e3w2q/Pangaea-keyboard/images/0a40776e85302190b7db8250a09605896cdc25e2c0a9c59730956f0daec5297e.jpg

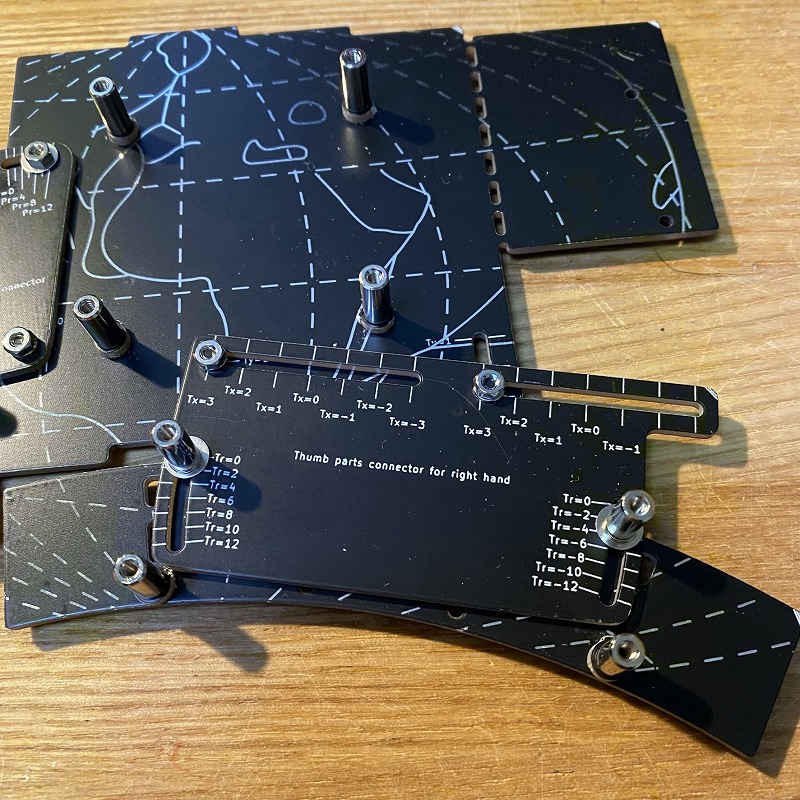
images/0a40776e85302190b7db8250a09605896cdc25e2c0a9c59730956f0daec5297e.jpg
