e3w2q/Pangaea-keyboard/images/3de5a38e3a6196bc59657bb92bddd8e8714a5d8ba0b0069f44ba43b166290112.jpg

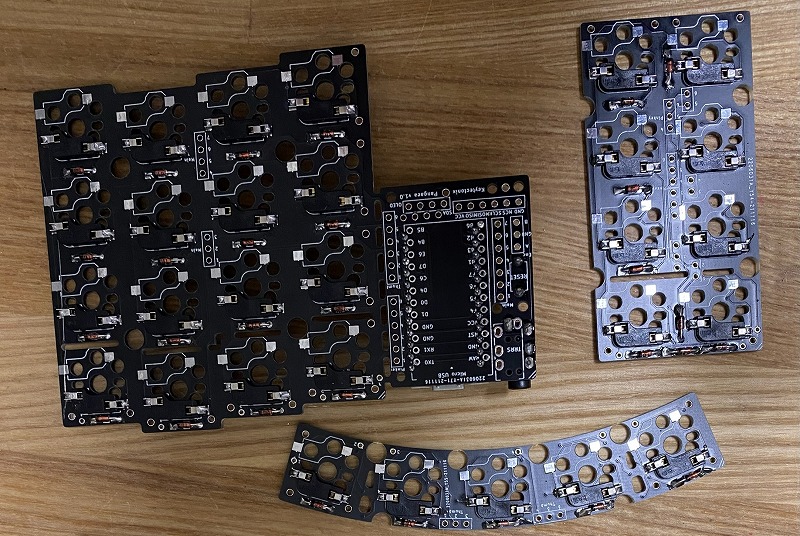
images/3de5a38e3a6196bc59657bb92bddd8e8714a5d8ba0b0069f44ba43b166290112.jpg
