e3w2q/Pangaea-keyboard/images/6bcce53f80934620b18218db5a653d9b1c7b2bb7c57de2113d1901ce5737880e.jpg

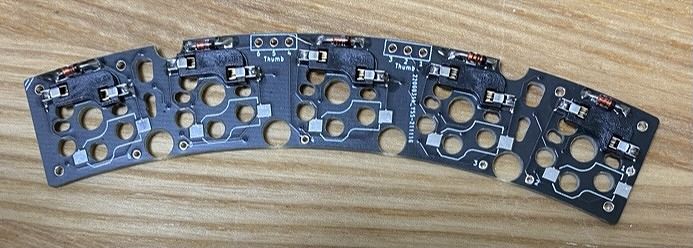
images/6bcce53f80934620b18218db5a653d9b1c7b2bb7c57de2113d1901ce5737880e.jpg
