e3w2q/Pangaea-keyboard/images/12b5d017e92538700fd86b66f8f17ba5b7837069fc4d05f0cf9e0c62a58a4044.jpg

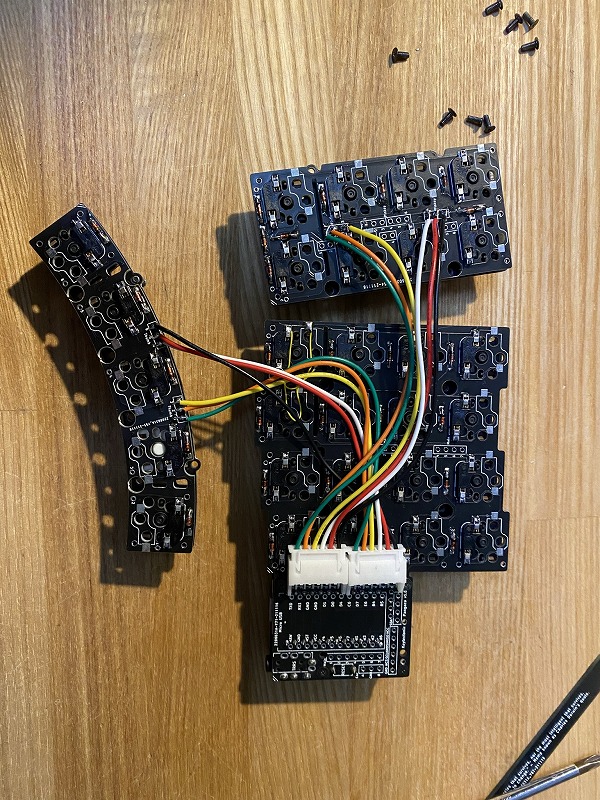
images/12b5d017e92538700fd86b66f8f17ba5b7837069fc4d05f0cf9e0c62a58a4044.jpg
