e3w2q/Pangaea-keyboard/images/13a6e4abe06fdf55e29f08c79a0a2a02d93426b52d6df6399b1b247043b9f3ee.jpg

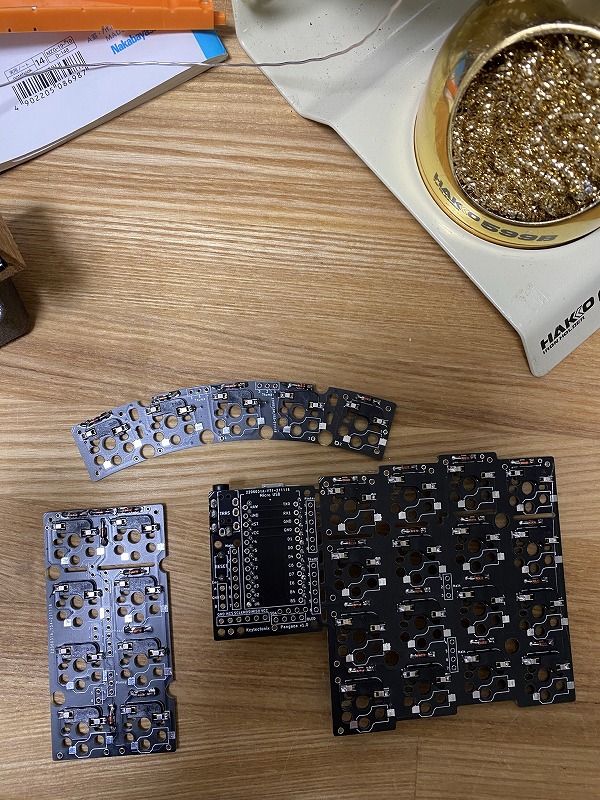
images/13a6e4abe06fdf55e29f08c79a0a2a02d93426b52d6df6399b1b247043b9f3ee.jpg
