e3w2q/Pangaea-keyboard/images/27a483f2cba5d88a76916c5f78700c6e7530f33930280dae4c5f8cfa2cd41bf4.jpg

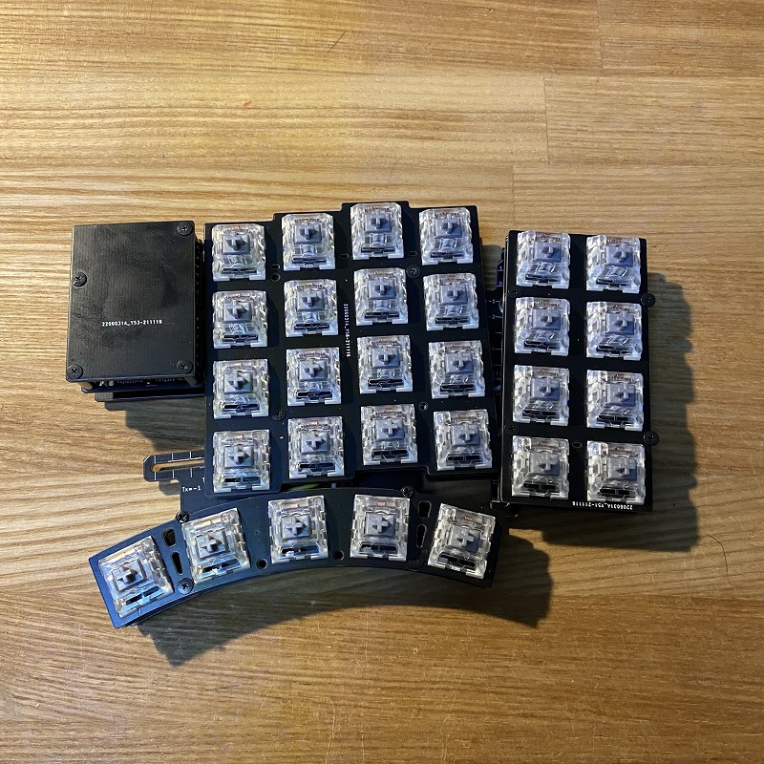
images/27a483f2cba5d88a76916c5f78700c6e7530f33930280dae4c5f8cfa2cd41bf4.jpg
