e3w2q/Pangaea-keyboard/images/60b84ec0d109d0ff8fc8ae6644fc2632dbbb4cfb449918cca01a9c03fa35eddc.jpg

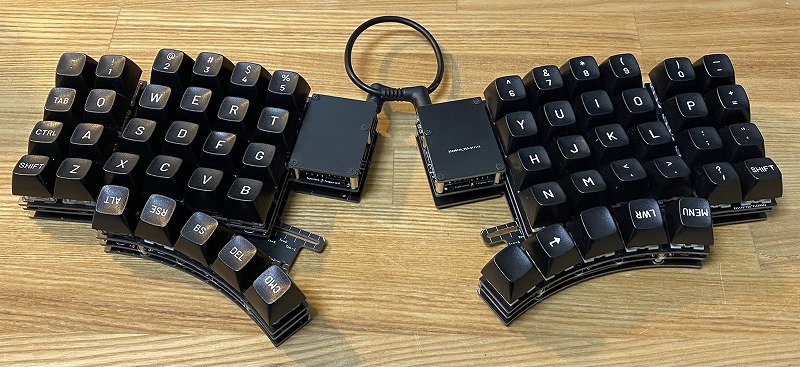
images/60b84ec0d109d0ff8fc8ae6644fc2632dbbb4cfb449918cca01a9c03fa35eddc.jpg
