e3w2q/Pangaea-keyboard/images/063d4ac2fd48cc3513ddb311a2d0394e6f6cdcdaa0d06b1ff0ed7a4a48f6335a.png

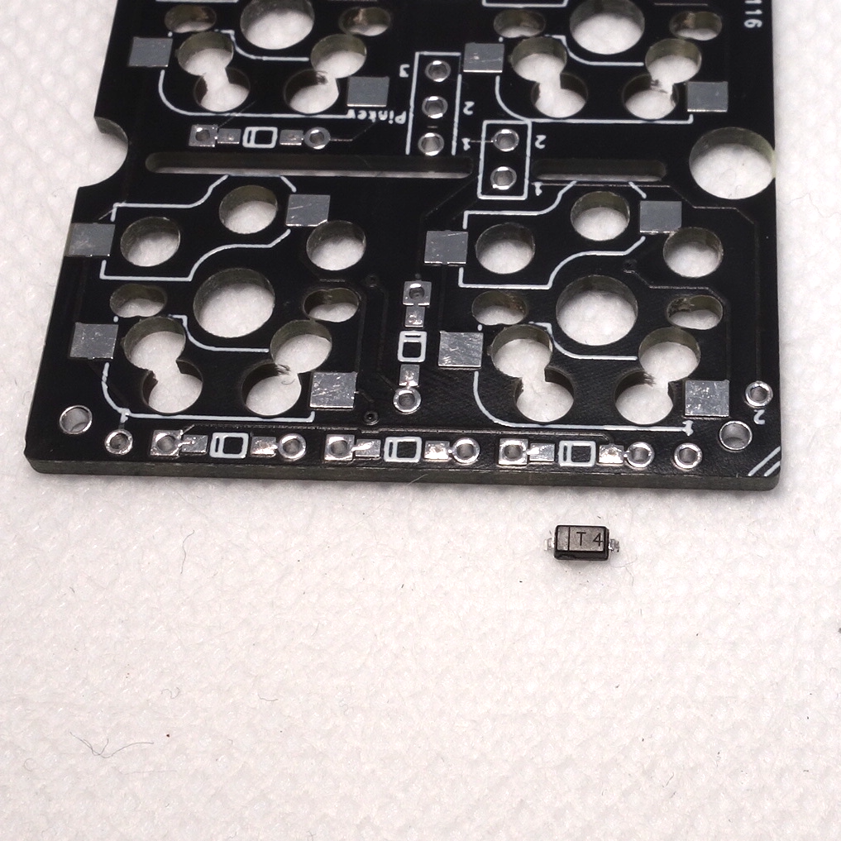
images/063d4ac2fd48cc3513ddb311a2d0394e6f6cdcdaa0d06b1ff0ed7a4a48f6335a.png
