e3w2q/Pangaea-keyboard/images/67ab104578fdced3b91575ca5da068cccac055a47365c25860a59a9be2ea70eb.jpg

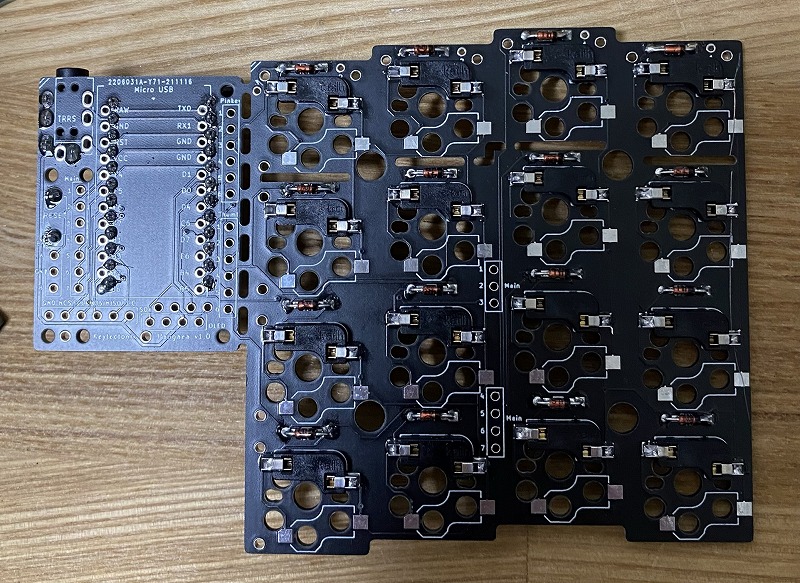
images/67ab104578fdced3b91575ca5da068cccac055a47365c25860a59a9be2ea70eb.jpg
