e3w2q/Pangaea-keyboard/images/92ce04aa23efa934309d4d564b36739e237e41bc6f97a7b27b288d3fab1753d2.jpg

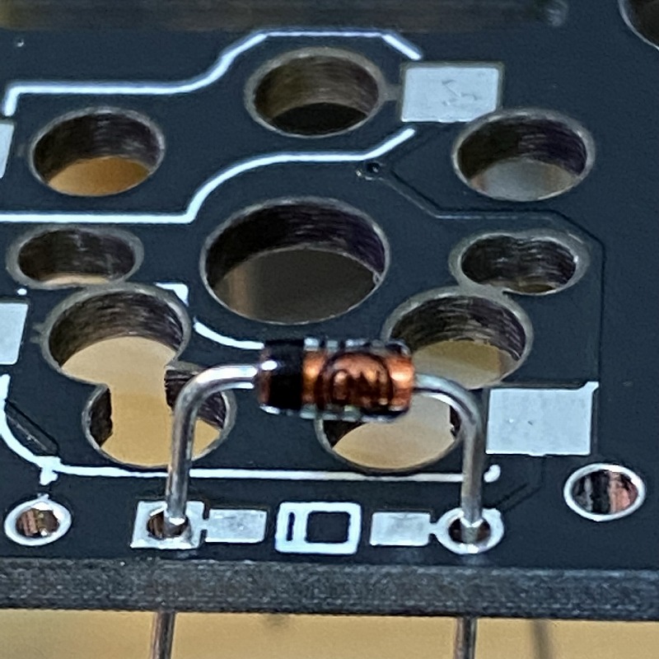
images/92ce04aa23efa934309d4d564b36739e237e41bc6f97a7b27b288d3fab1753d2.jpg
