e3w2q/Pangaea-keyboard/images/265e11b32b4d3e79da52cd56ff77c7da640a06a07a428f72cf4426d7e051b964.jpg

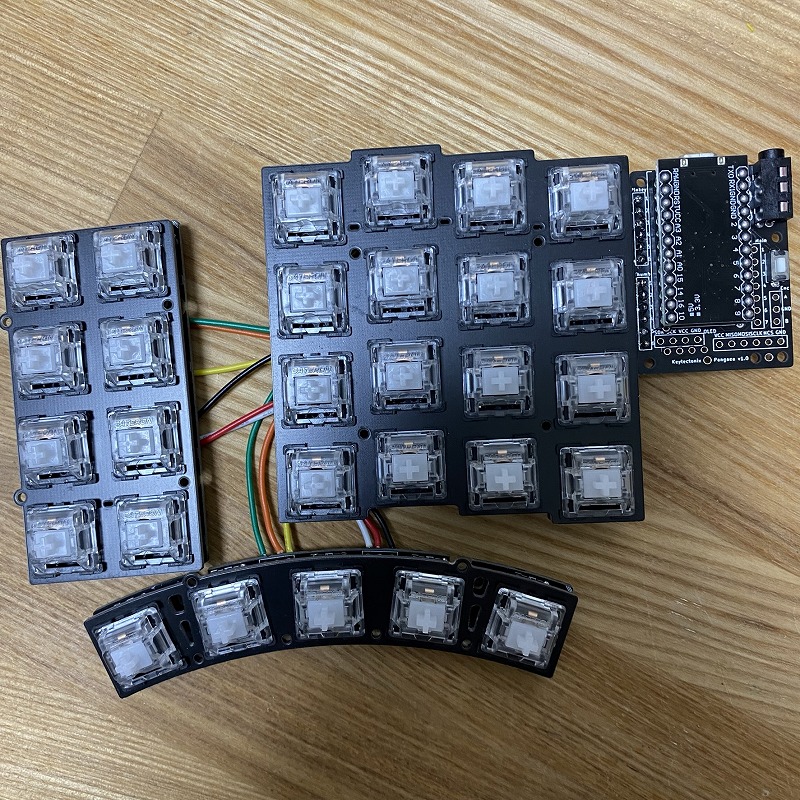
images/265e11b32b4d3e79da52cd56ff77c7da640a06a07a428f72cf4426d7e051b964.jpg
