e3w2q/Pangaea-keyboard/images/1651ed1e01f4abee588f21293dc81c73a5ee6cbbf57d6cacc2041a118a28469f.png

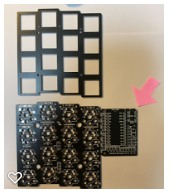
images/1651ed1e01f4abee588f21293dc81c73a5ee6cbbf57d6cacc2041a118a28469f.png
