e3w2q/Pangaea-keyboard/images/4654de285b3f48fc8ee407a733680955d16ebc803d51c34f99765b41f4ffe5e8.jpg

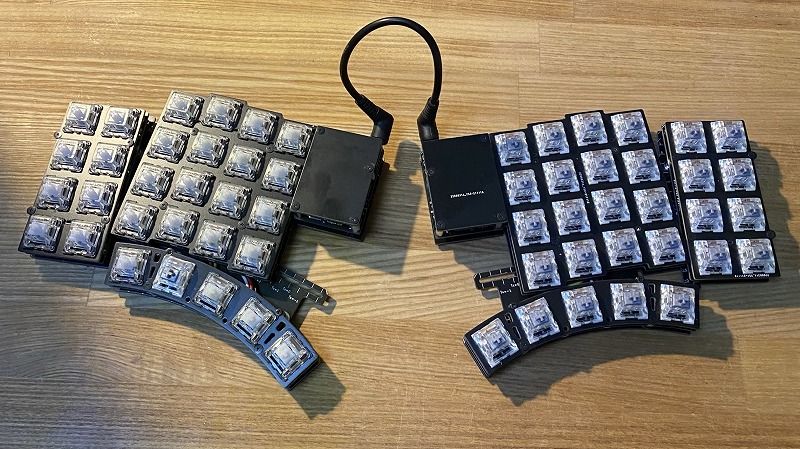
images/4654de285b3f48fc8ee407a733680955d16ebc803d51c34f99765b41f4ffe5e8.jpg
