e3w2q/Pangaea-keyboard/images/7964ab9c6218b75f5bff196d36406f74450f77bdc9f00a825abc09a86ed46ff9.jpg

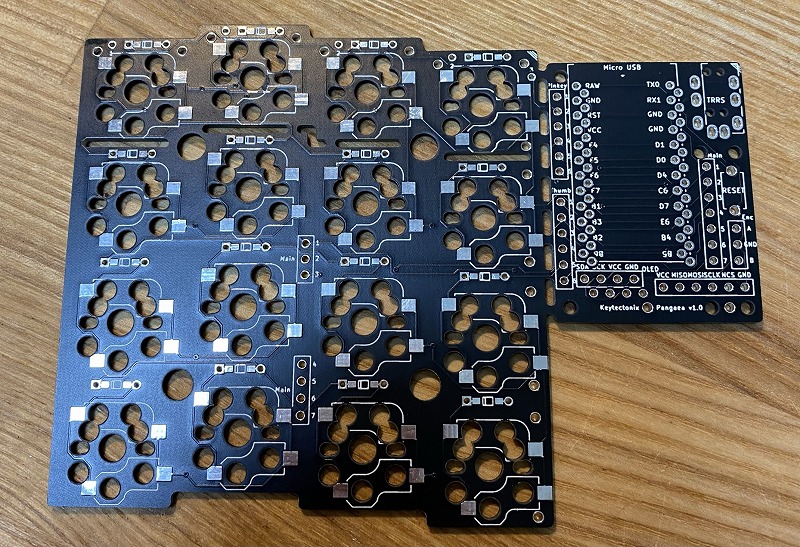
images/7964ab9c6218b75f5bff196d36406f74450f77bdc9f00a825abc09a86ed46ff9.jpg
