e3w2q/Pangaea-keyboard/images/15282b31c44fe6ef8862abb38c801023dfbcf05c0192a9374a89fd2af4d39e05.jpg

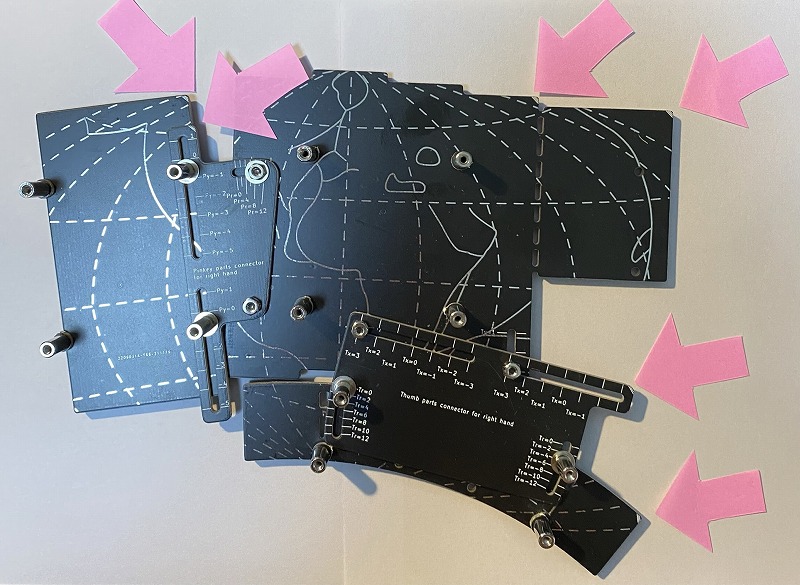
images/15282b31c44fe6ef8862abb38c801023dfbcf05c0192a9374a89fd2af4d39e05.jpg
