e3w2q/Pangaea-keyboard/images/0477079cc677149b845d37c62d5b3265d9a6df82ff215ac21fa13e02ba05858f.png

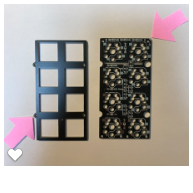
images/0477079cc677149b845d37c62d5b3265d9a6df82ff215ac21fa13e02ba05858f.png
