e3w2q/Pangaea-keyboard/images/0908893b698defab134e45d7c74e45a14b349f7c2ef67a782a992773b4fd4b19.jpg

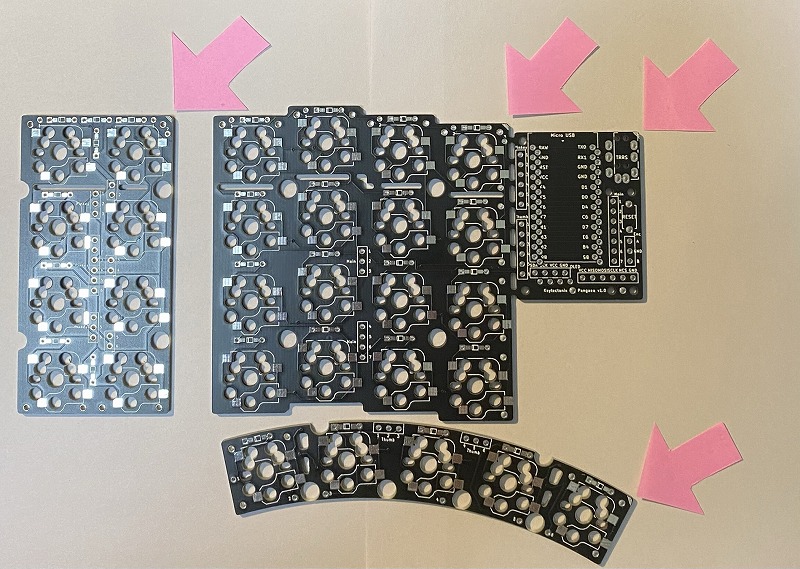
images/0908893b698defab134e45d7c74e45a14b349f7c2ef67a782a992773b4fd4b19.jpg
