e3w2q/Pangaea-keyboard/images/965143ae04164a4b04ba0ac7c3d9436b181fd4520849607ac215952e7ac29c34.jpg

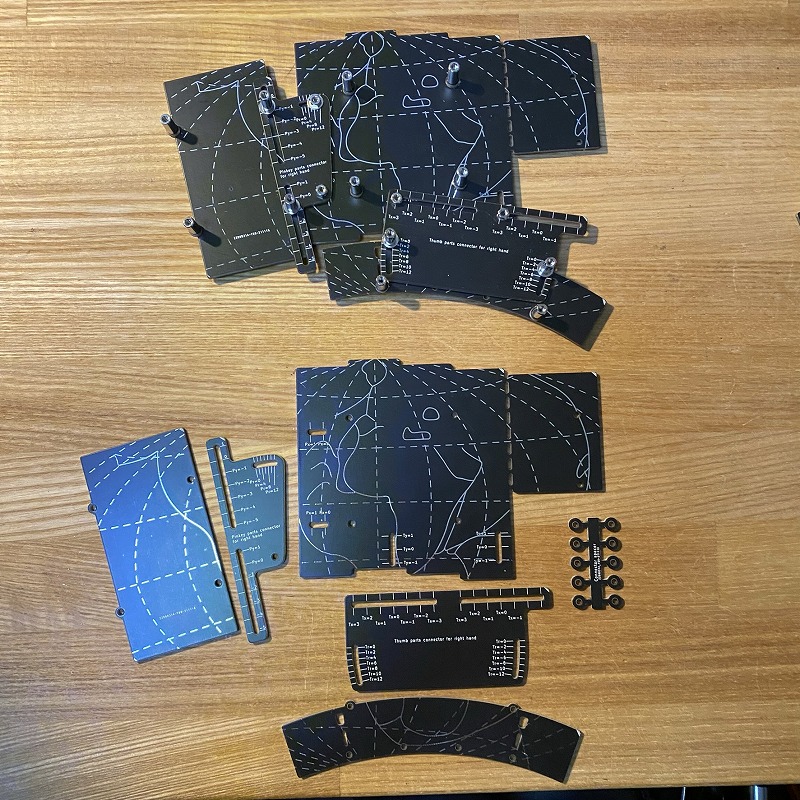
images/965143ae04164a4b04ba0ac7c3d9436b181fd4520849607ac215952e7ac29c34.jpg
