e3w2q/Pangaea-keyboard/images/ae8b663de61265fc9e2a7c73a48820bda330f6d65dd7c69996d7fd06cbfcfd85.jpg

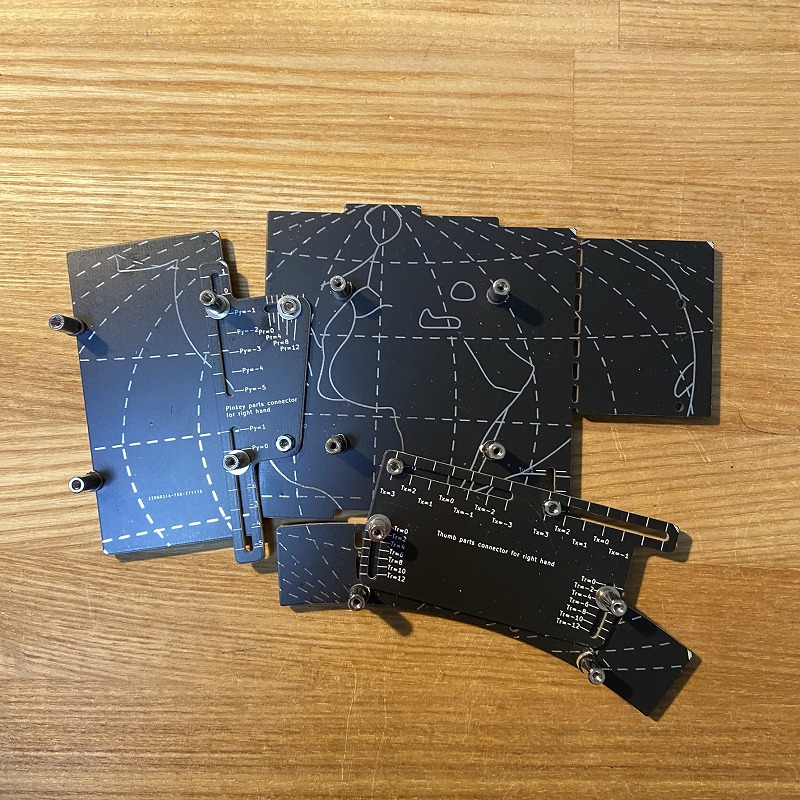
images/ae8b663de61265fc9e2a7c73a48820bda330f6d65dd7c69996d7fd06cbfcfd85.jpg
