e3w2q/Pangaea-keyboard/images/b1e843c930b5d5a4a3331d23bac49f055a0c1e8cba4a9a129905668647902217.jpg

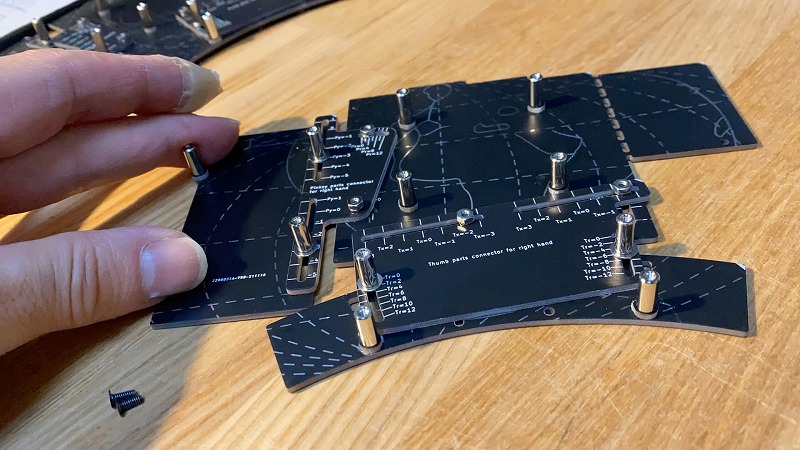
images/b1e843c930b5d5a4a3331d23bac49f055a0c1e8cba4a9a129905668647902217.jpg
