e3w2q/Pangaea-keyboard/images/d9ac8d5ce5317f976f2c17d7057b1348e89b5a3f5772f75e08f726dfaba970bf.jpg

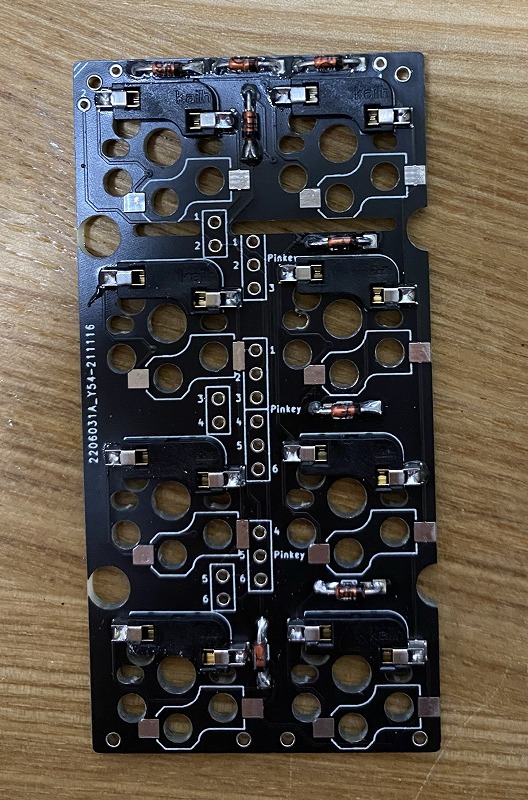
images/d9ac8d5ce5317f976f2c17d7057b1348e89b5a3f5772f75e08f726dfaba970bf.jpg
