e3w2q/Pangaea-keyboard/images/d27c56cb22e5b8cc0af3af3c9623e22fa6d8d71f143a236a87373760cafe7f19.png

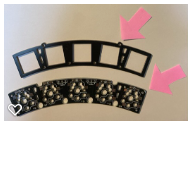
images/d27c56cb22e5b8cc0af3af3c9623e22fa6d8d71f143a236a87373760cafe7f19.png
