e3w2q/Pangaea-keyboard/images/d383ae3981553dc0fcf38ef8d6c3e6acfb4eb097b5aa347cb851257b4d14731c.jpg

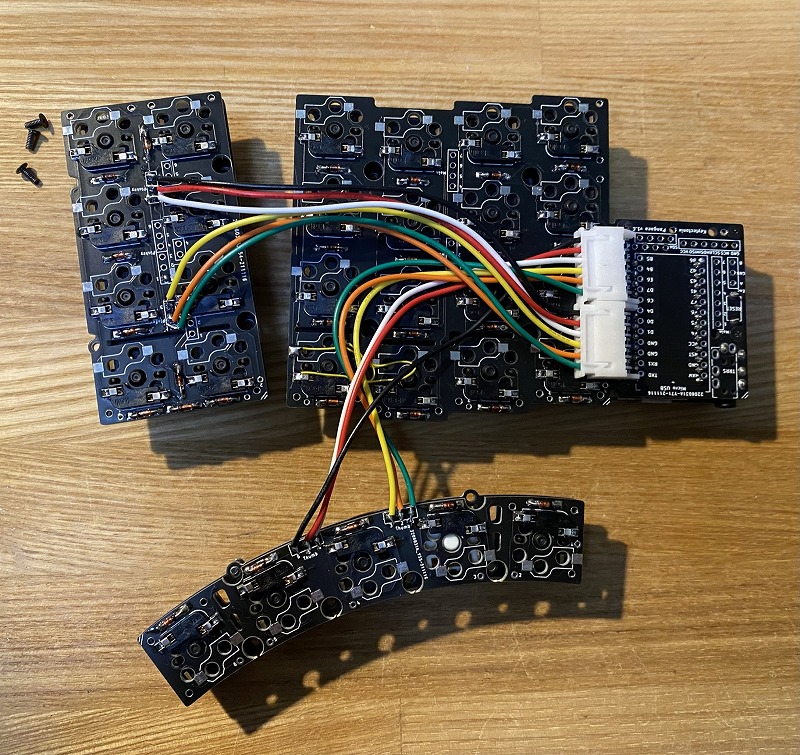
images/d383ae3981553dc0fcf38ef8d6c3e6acfb4eb097b5aa347cb851257b4d14731c.jpg
