e3w2q/Pangaea-keyboard/images/d52466fd30a9bd447ba011db17c6af2e1d6d6b381e681eb9b976b4c6a248406f.jpg

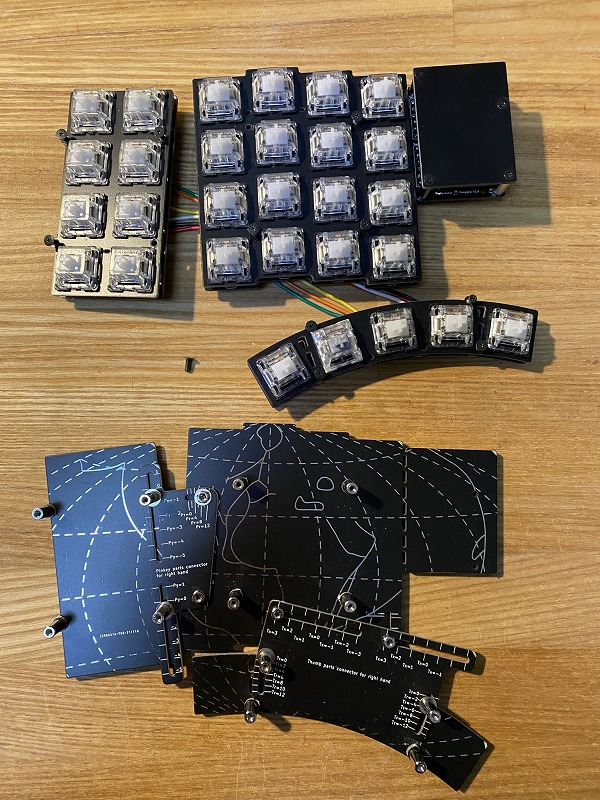
images/d52466fd30a9bd447ba011db17c6af2e1d6d6b381e681eb9b976b4c6a248406f.jpg
