e3w2q/Pangaea-keyboard/images/db102ce236ea3b06e92ff9be887bdc986abb1811367a4291042e3f9954540378.png

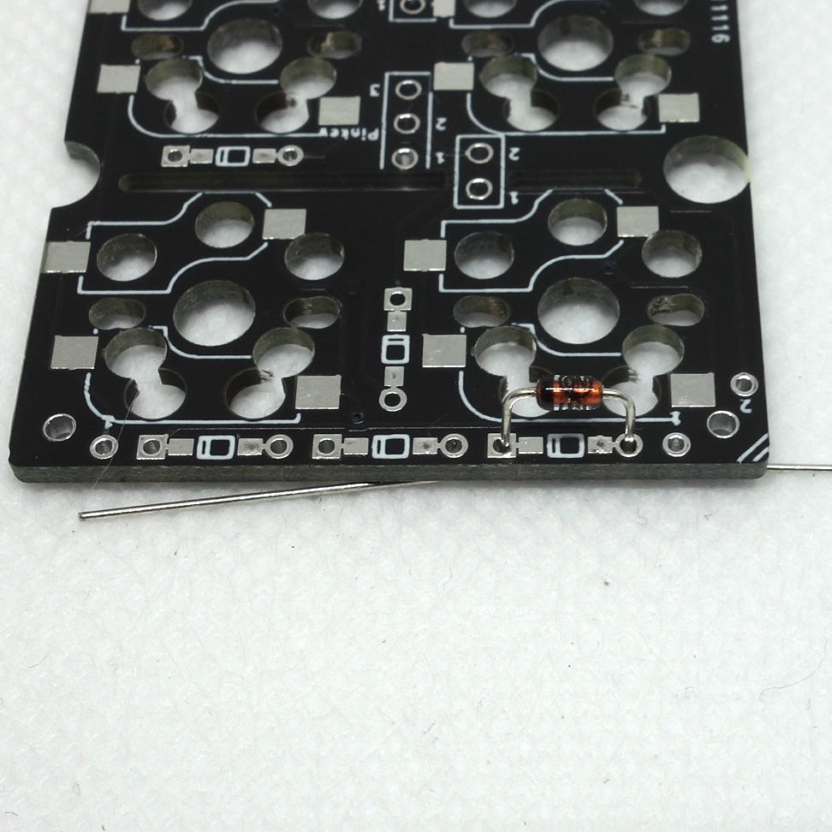
images/db102ce236ea3b06e92ff9be887bdc986abb1811367a4291042e3f9954540378.png
