e3w2q/Pangaea-keyboard/images/DSCF6513.jpeg

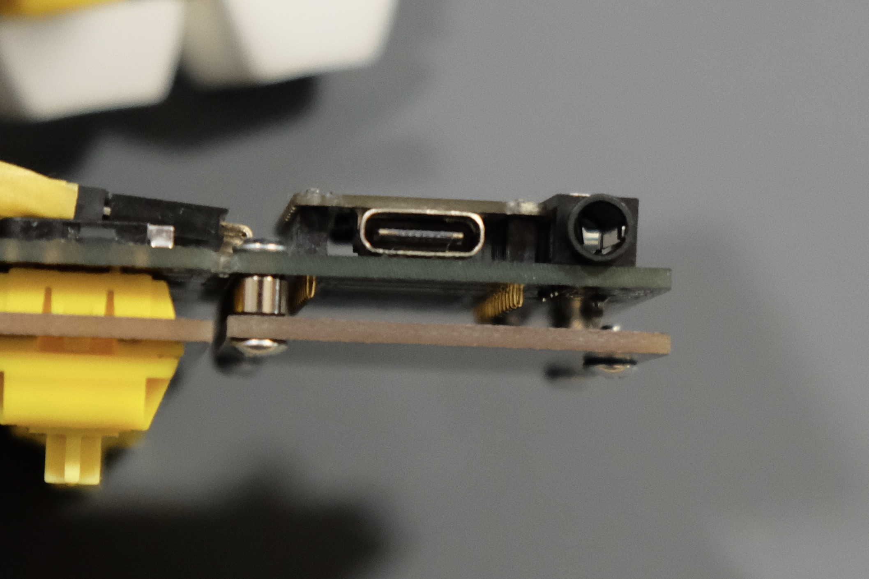
images/DSCF6513.jpeg
