e3w2q/Pangaea-keyboard/images/DSCF8427.jpg

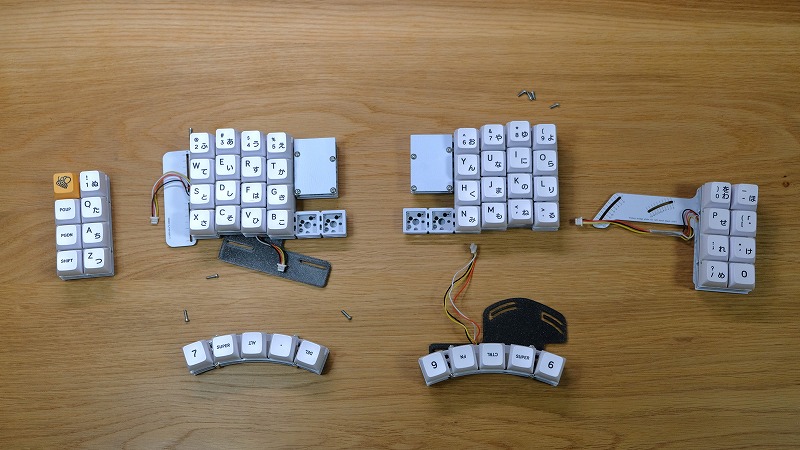
images/DSCF8427.jpg
