e3w2q/Pangaea-keyboard/images/DSCF8429.jpg

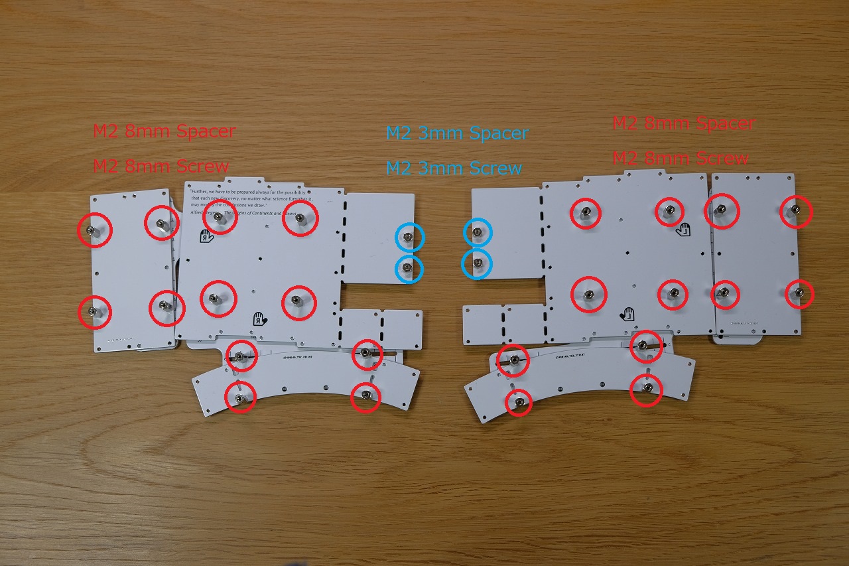
images/DSCF8429.jpg
