e3w2q/Pangaea-keyboard/images/DSCF8474.jpg

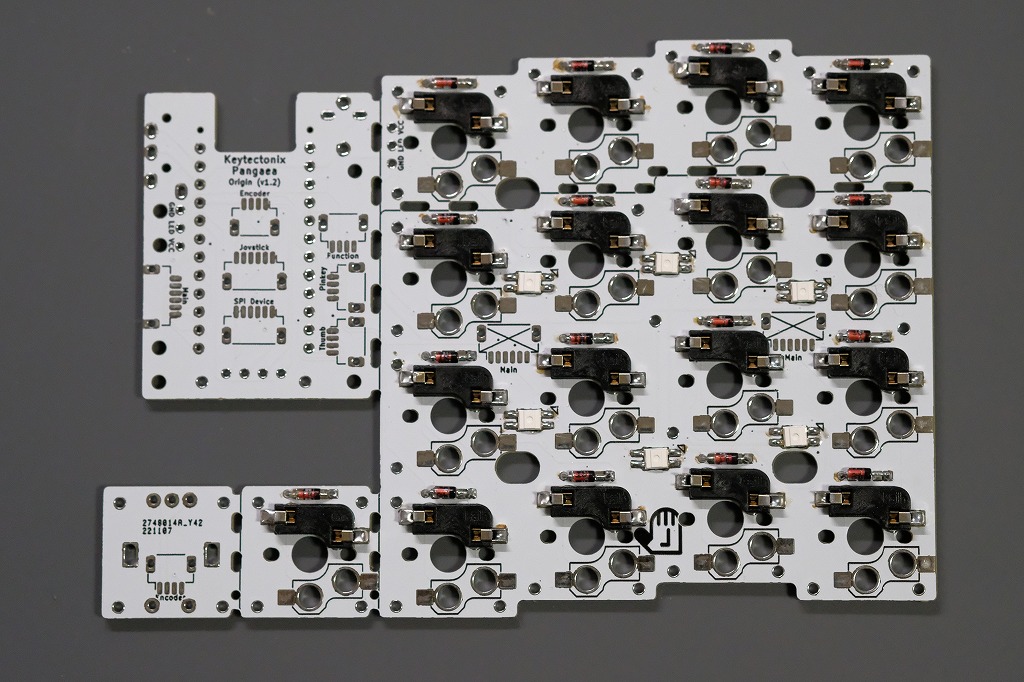
images/DSCF8474.jpg
