e3w2q/Pangaea-keyboard/images/DSCF8711.jpg

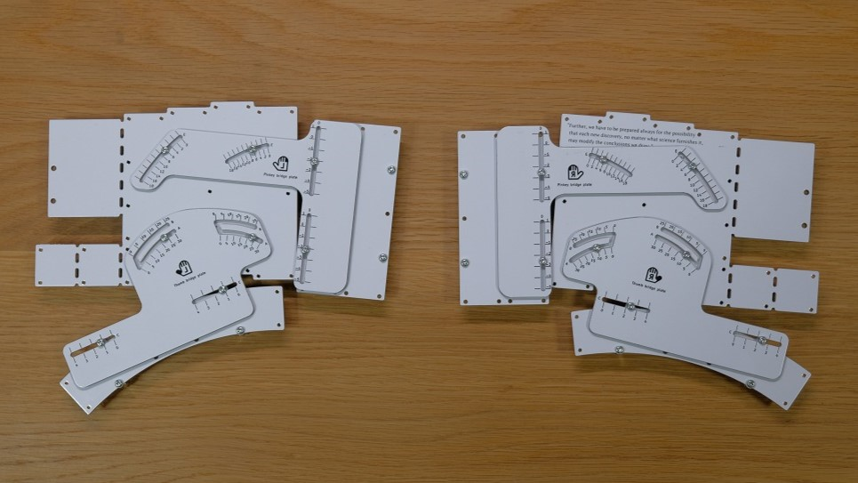
images/DSCF8711.jpg
