e3w2q/Pangaea-keyboard/images/e3-all.jpg

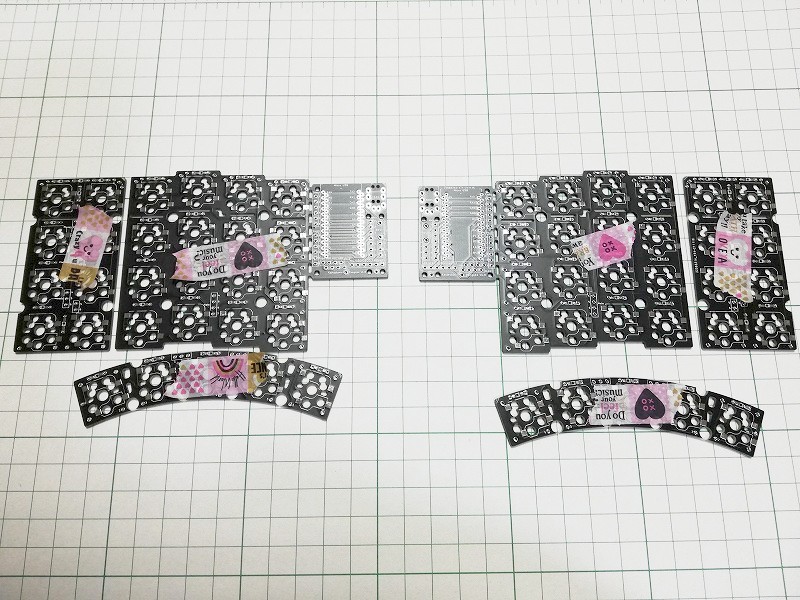
images/e3-all.jpg
