e3w2q/Pangaea-keyboard/images/e3-left.jpg

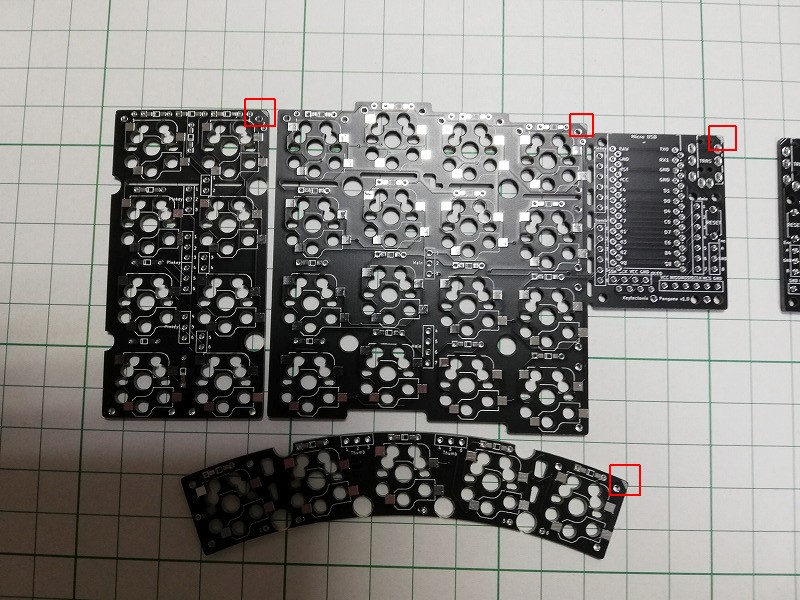
images/e3-left.jpg
