e3w2q/Pangaea-keyboard/images/e3-promicro.jpg

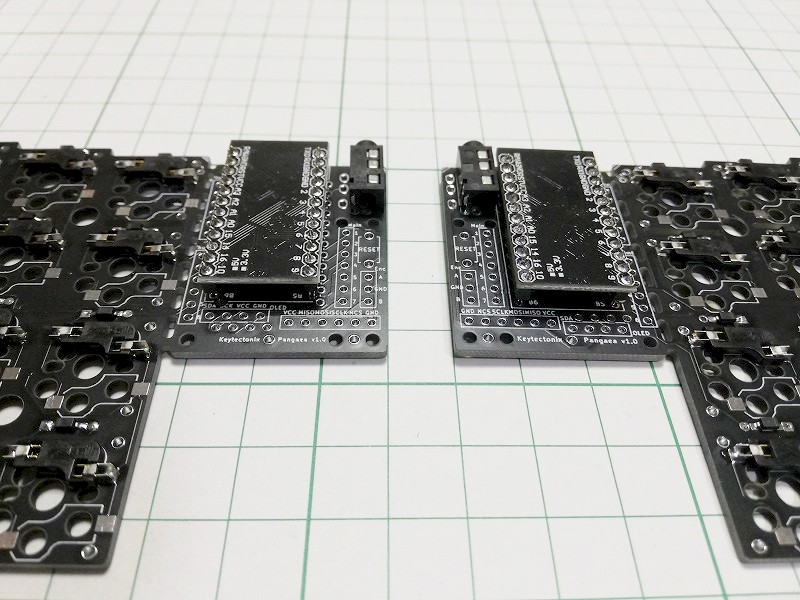
images/e3-promicro.jpg
