e3w2q/Pangaea-keyboard/images/e3-right.jpg

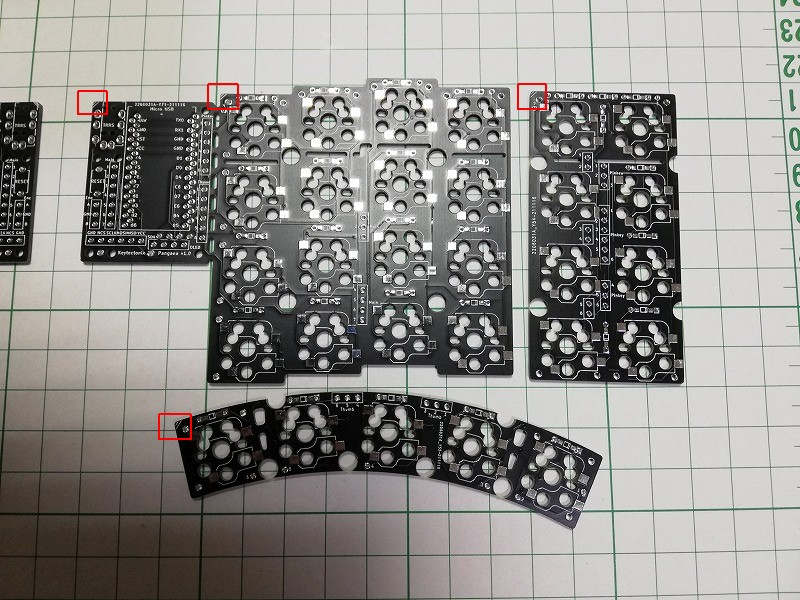
images/e3-right.jpg
