e3w2q/Pangaea-keyboard/images/e3-trrs.jpg

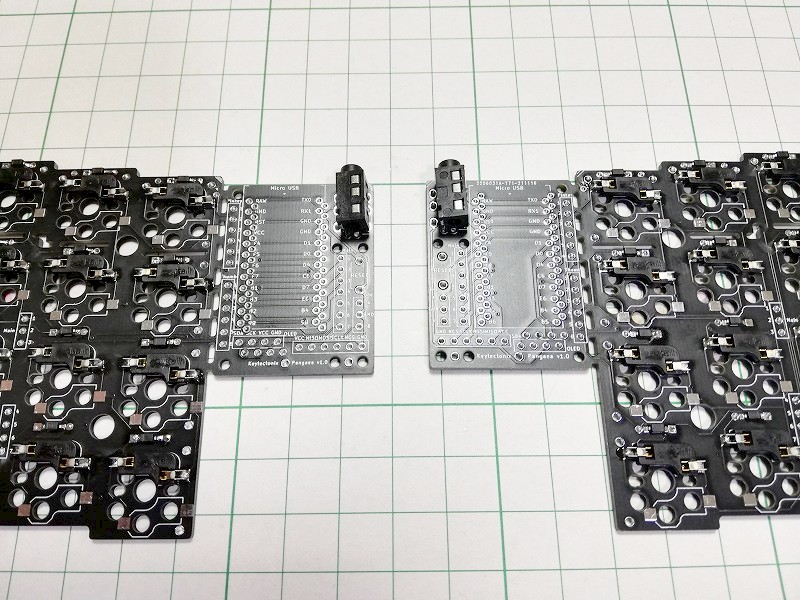
images/e3-trrs.jpg
