e3w2q/Pangaea-keyboard/images/f9d4656426ad7f02eab65f9deb88ad912d23467ad16db4615ea33113088e97a7.png

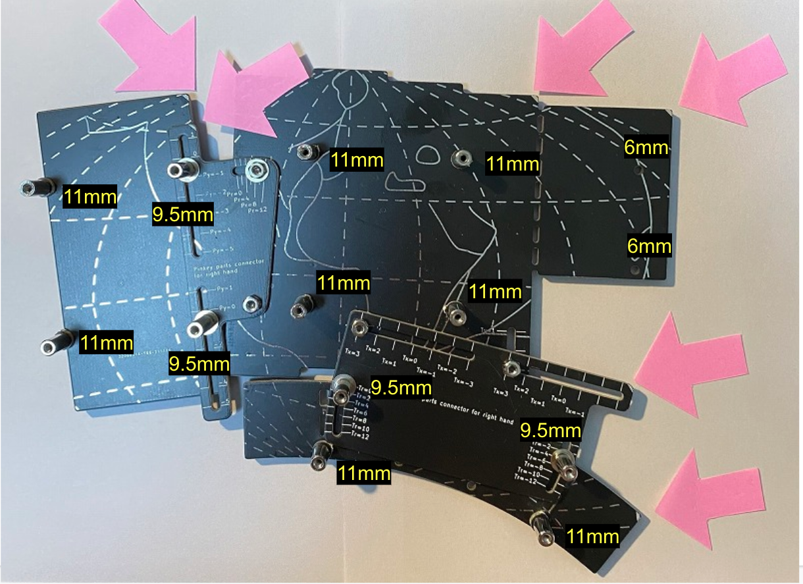
images/f9d4656426ad7f02eab65f9deb88ad912d23467ad16db4615ea33113088e97a7.png
