e3w2q/Pangaea-keyboard/images/f13e1266644263a3237f0dc3debcd90be7cba8184b91f7bf281d1283899af6be.jpg

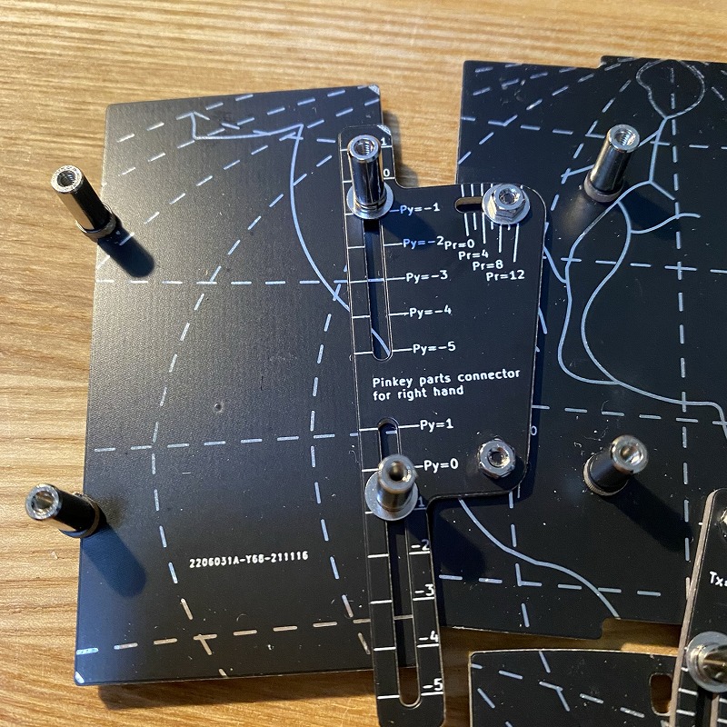
images/f13e1266644263a3237f0dc3debcd90be7cba8184b91f7bf281d1283899af6be.jpg
