e3w2q/Pangaea-keyboard/images/IMG_3902.jpeg

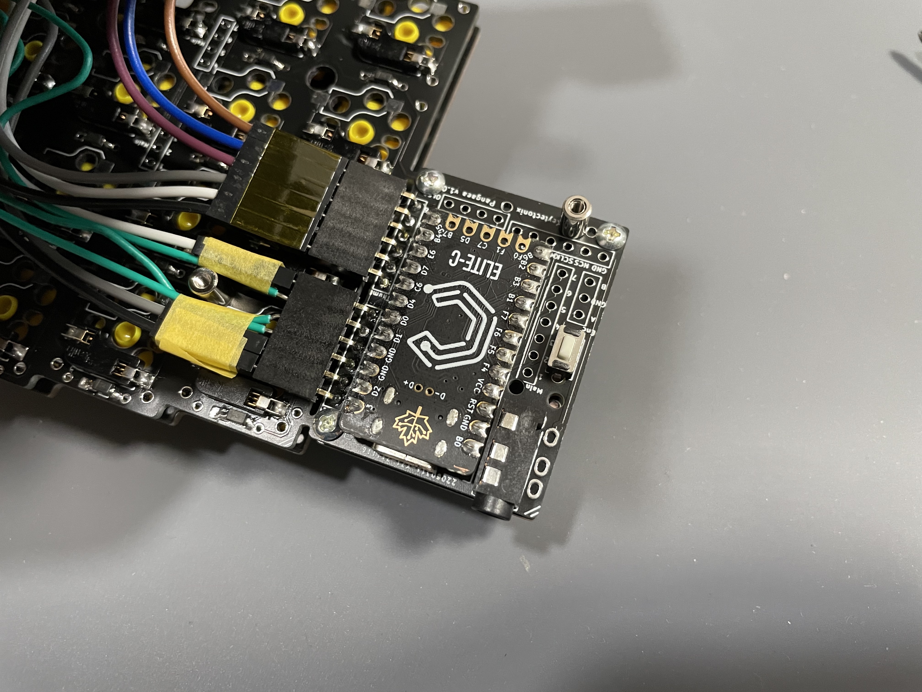
images/IMG_3902.jpeg
