e3w2q/Pangaea-keyboard/images/IMG_3923.jpeg

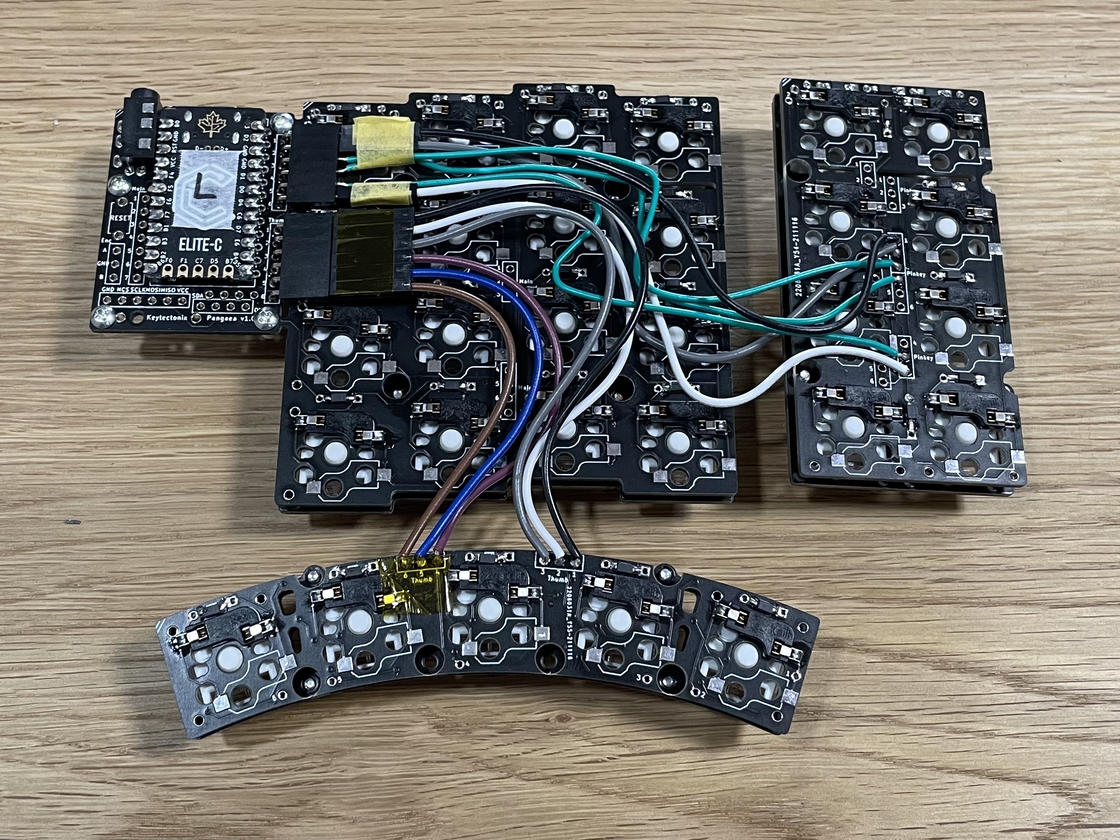
images/IMG_3923.jpeg
