e3w2q/Pangaea-keyboard/images/IMG_3924.jpeg

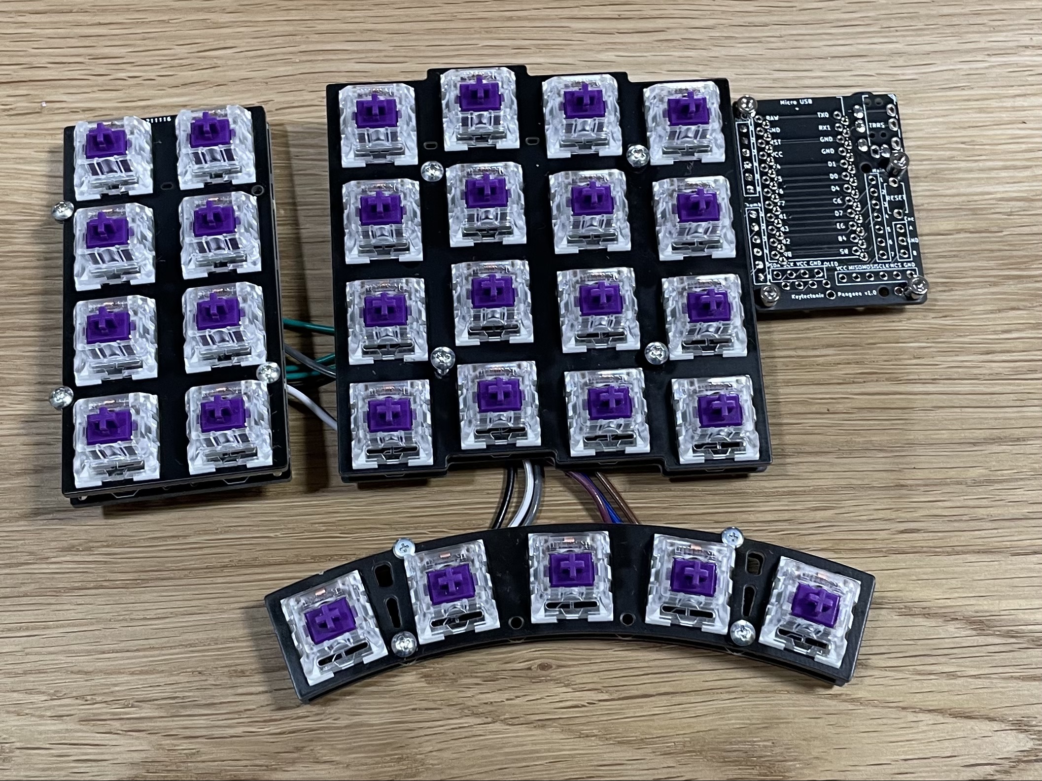
images/IMG_3924.jpeg
