e3w2q/Pangaea-keyboard/images/IMG_3925.jpeg

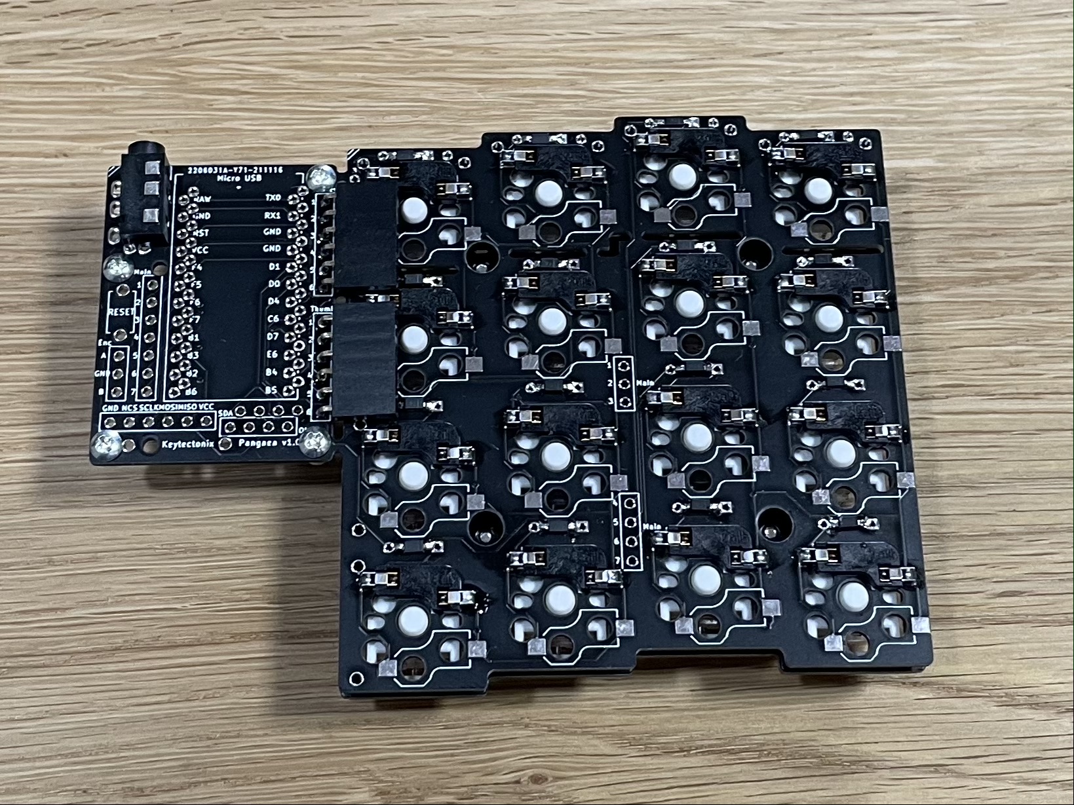
images/IMG_3925.jpeg
