e3w2q/Pangaea-keyboard/images/IMG_9328.jpg

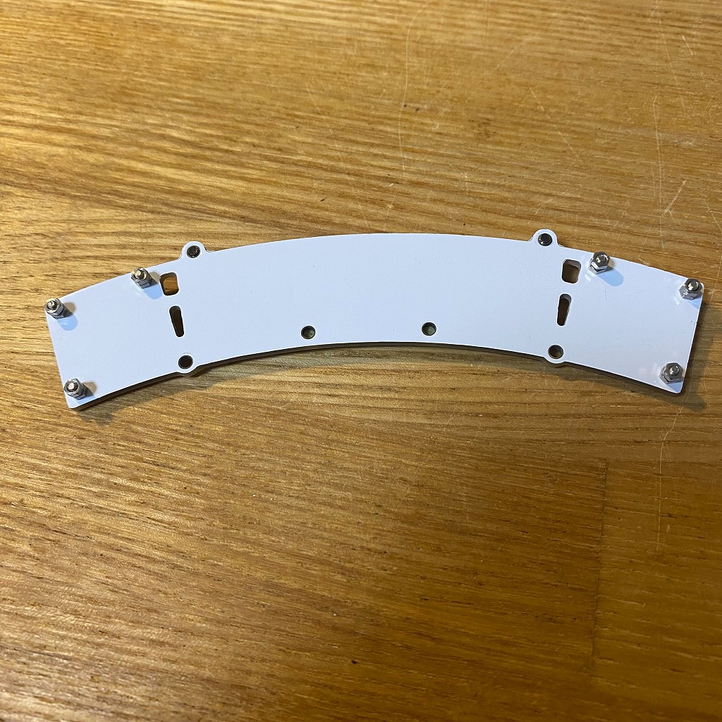
images/IMG_9328.jpg
