e3w2q/Pangaea-keyboard/images/IMG_9330.jpg

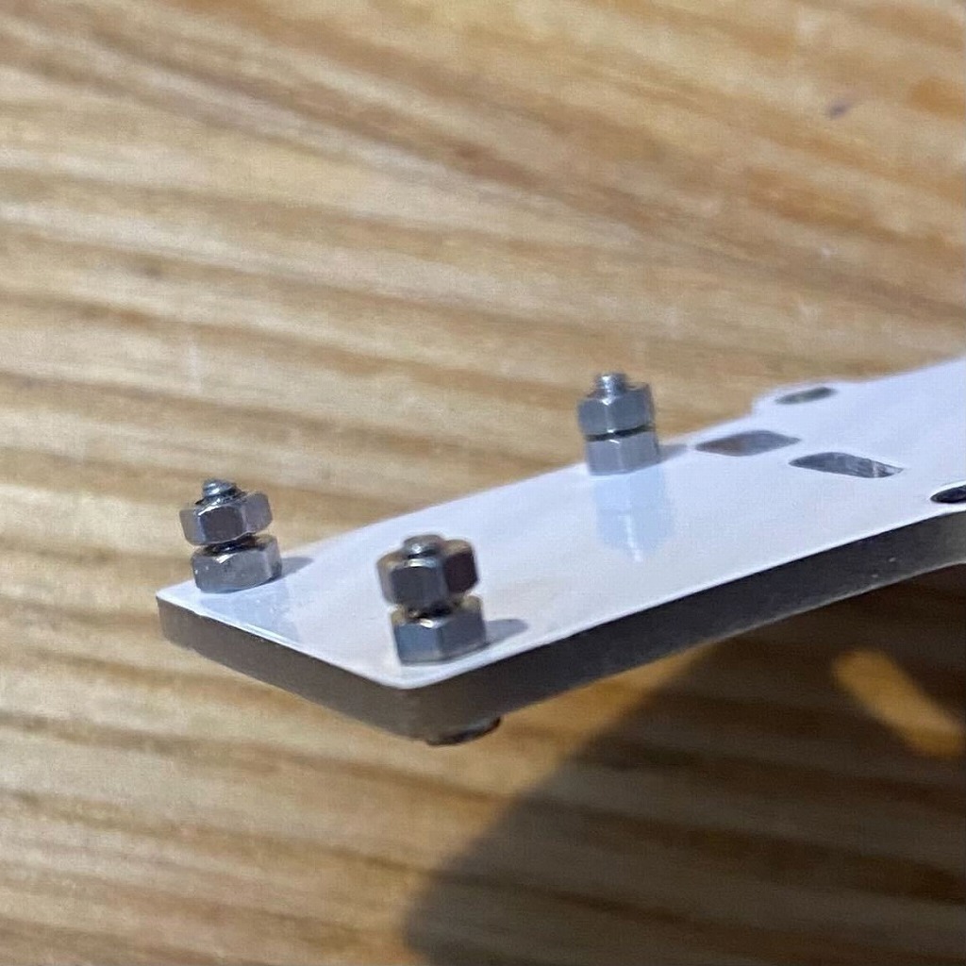
images/IMG_9330.jpg
