e3w2q/Pangaea-keyboard/images/pangaea_map1.png

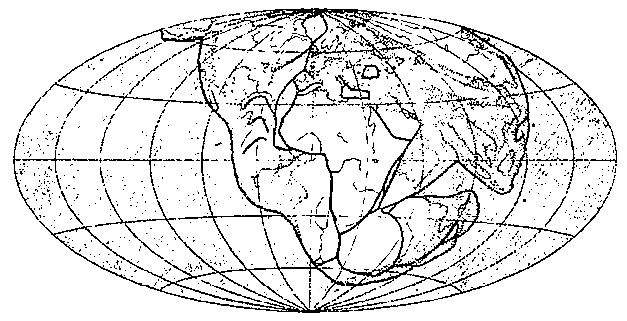
images/pangaea_map1.png
