e3w2q/Pangaea-keyboard/images/pangaea_map2.png

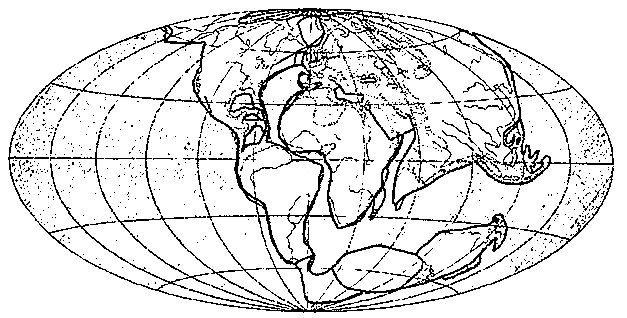
images/pangaea_map2.png
