e3w2q/Pangaea-keyboard/images/pangaea_v010.jpg

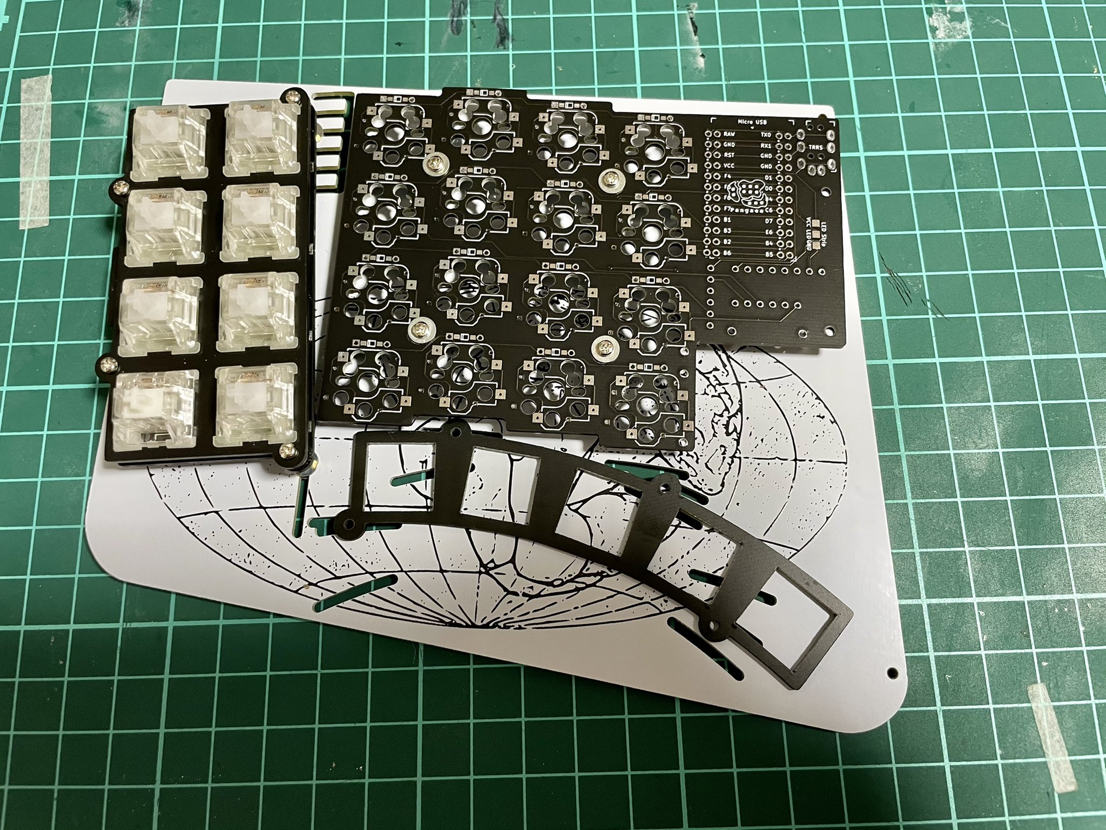
images/pangaea_v010.jpg
