e3w2q/Pangaea-keyboard/images/pangaea_v010_2.jpg

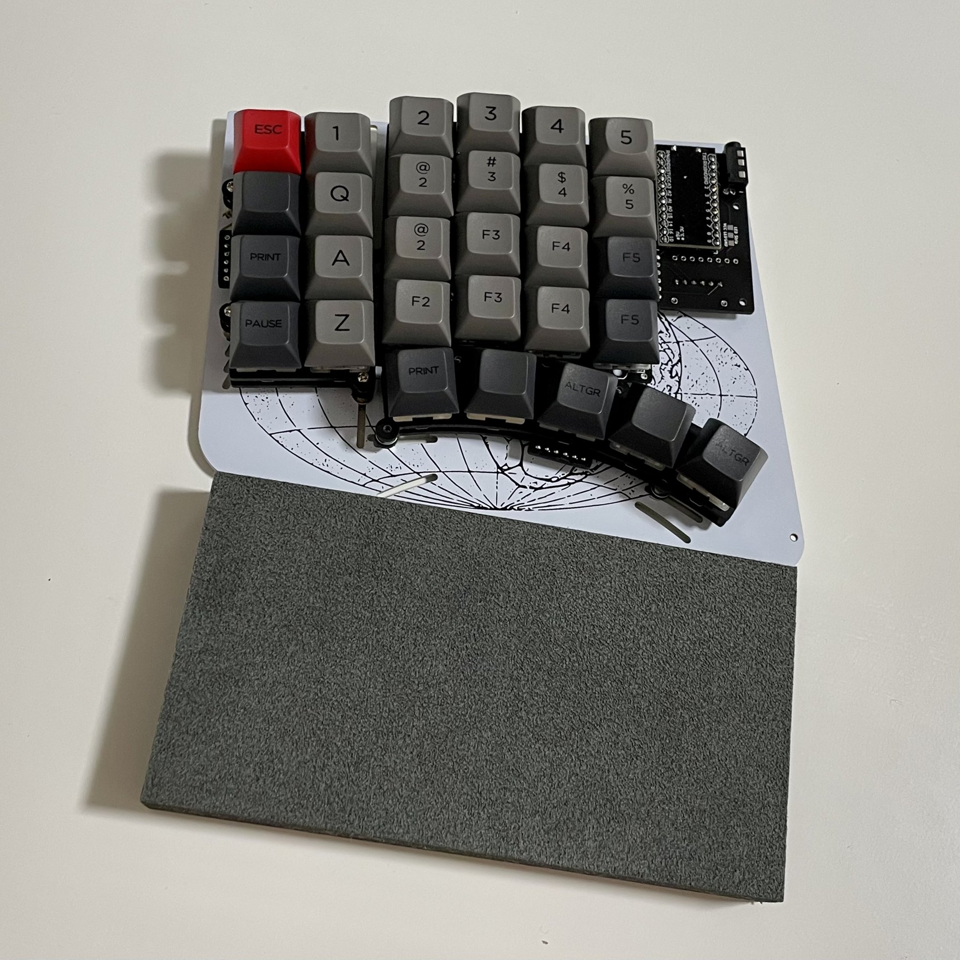
images/pangaea_v010_2.jpg
