e3w2q/Pangaea-keyboard/images/pangaea_v027_by_k2.jpg

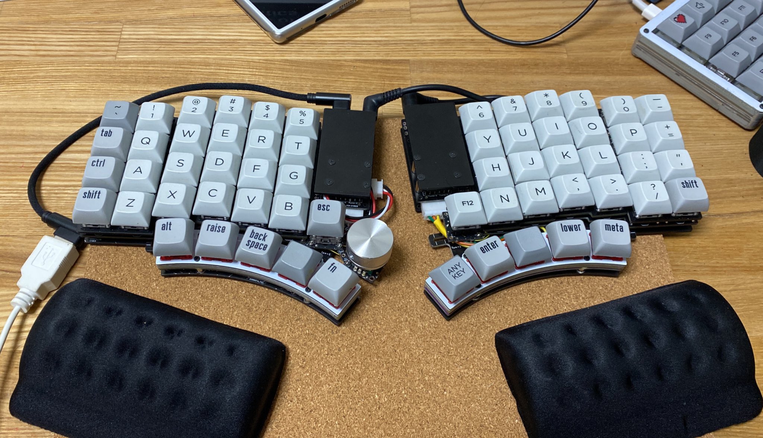
images/pangaea_v027_by_k2.jpg
