e3w2q/Pangaea-keyboard/images/pangaea_v027_by_same_2.jpg

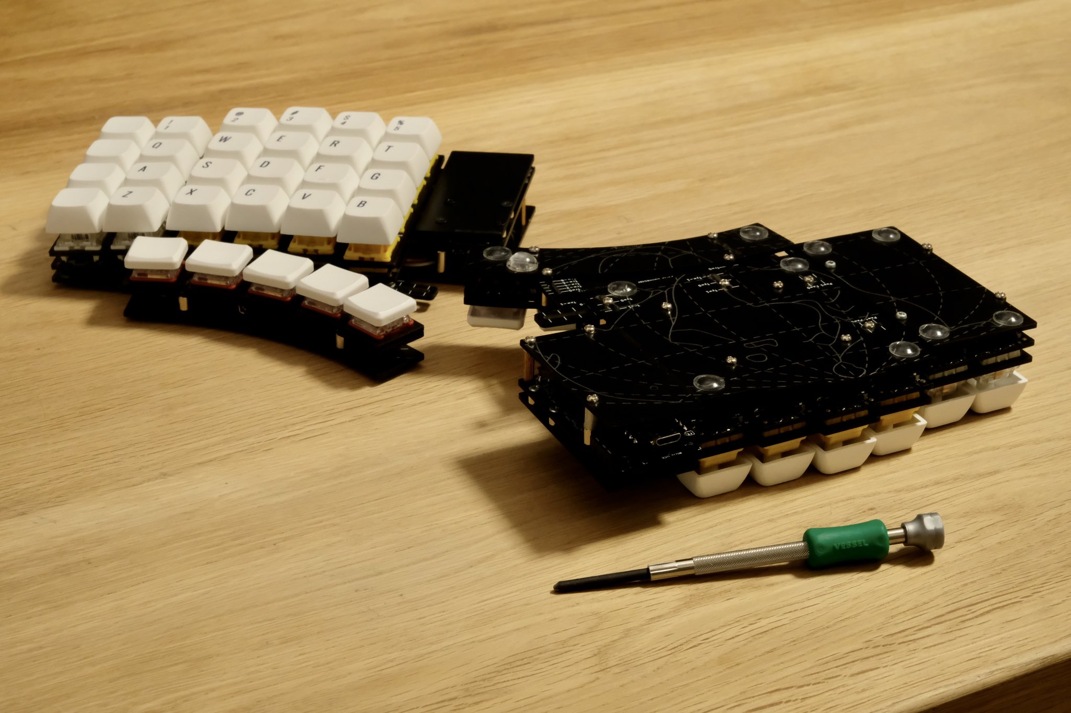
images/pangaea_v027_by_same_2.jpg
