e3w2q/Pangaea-keyboard/images/promicro_adhesive_prepare.jpg

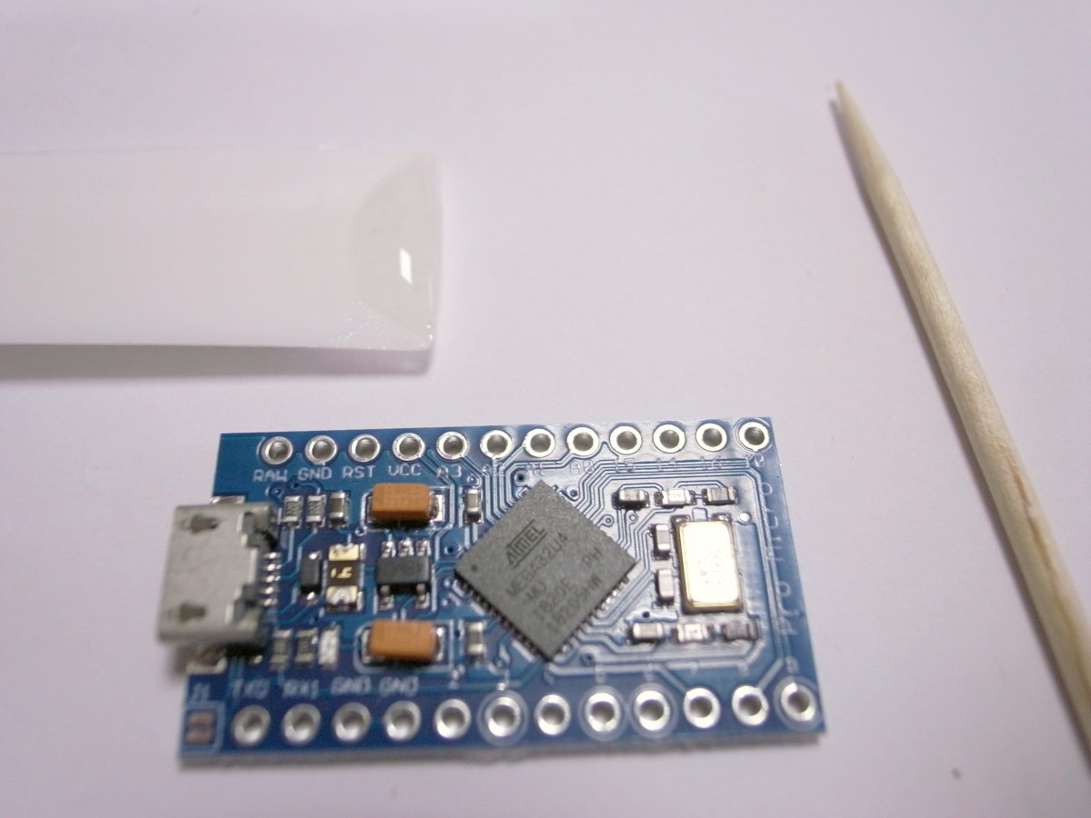
images/promicro_adhesive_prepare.jpg
