e3w2q/Pangaea-keyboard/images/promicro_pate.jpg

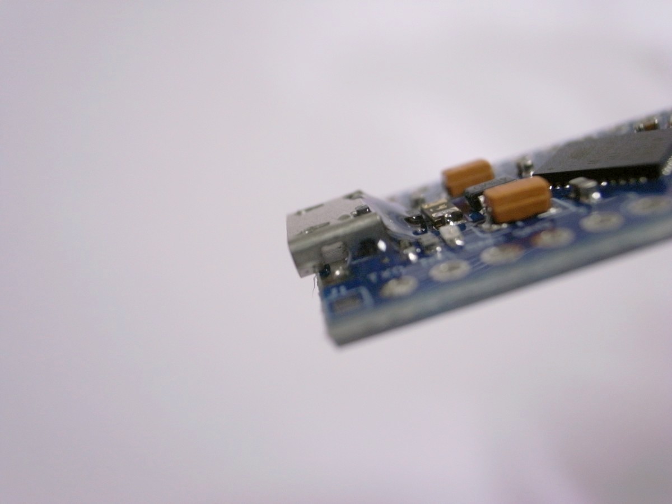
images/promicro_pate.jpg
