e3w2q/Pangaea-keyboard/images/promicro_stand.jpg

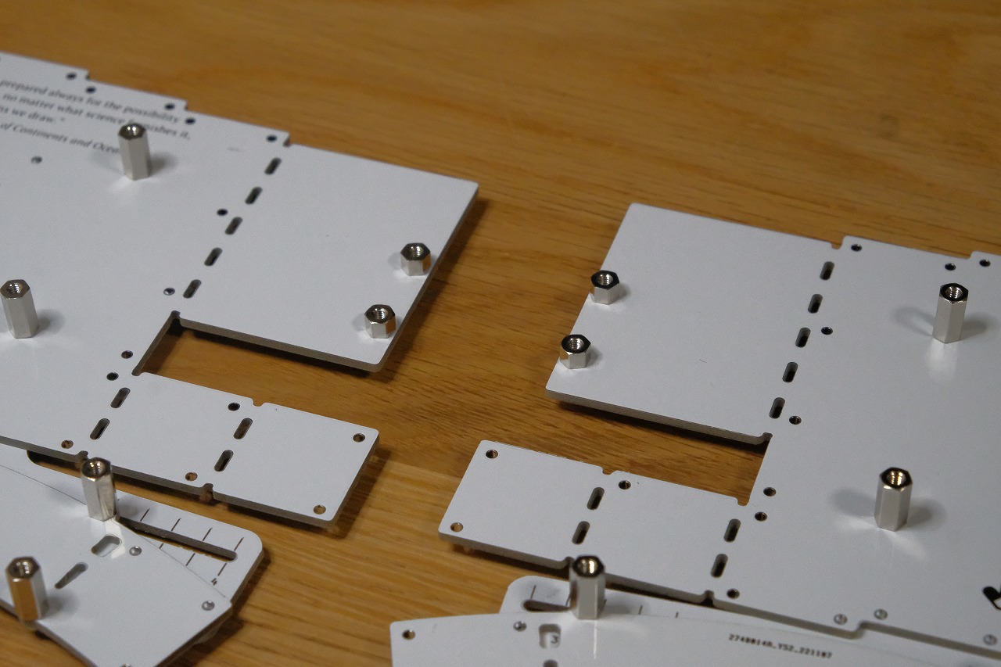
images/promicro_stand.jpg
