e3w2q/Pangaea-keyboard/images/quick2.jpeg

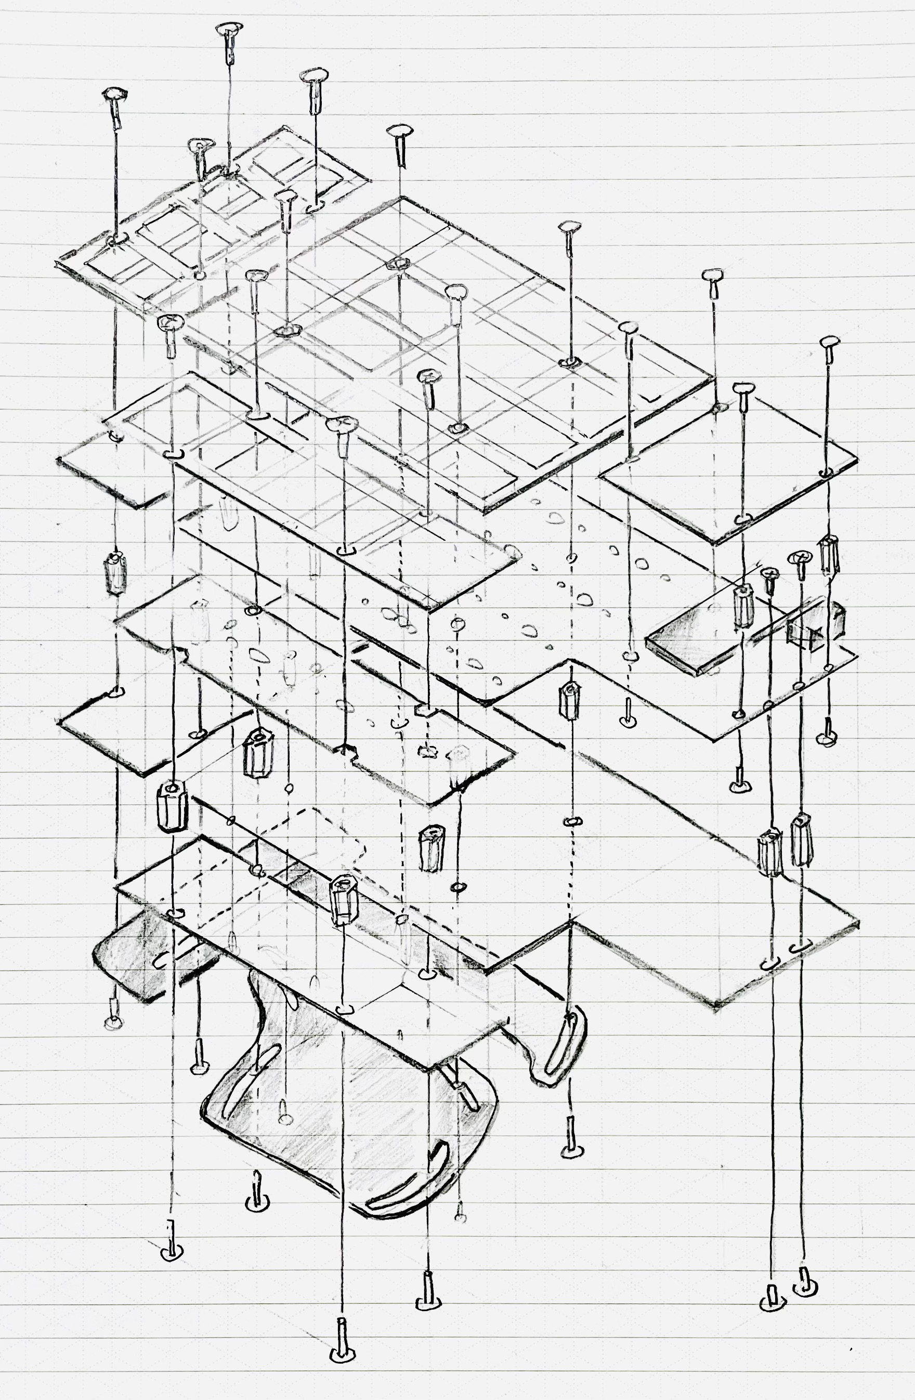
images/quick2.jpeg
