e3w2q/Pangaea-keyboard/design/pangaea_origin/pangaea.kicad_sch

## KiCad design design/pangaea_origin/pangaea.kicad_sch (2022-12-24)

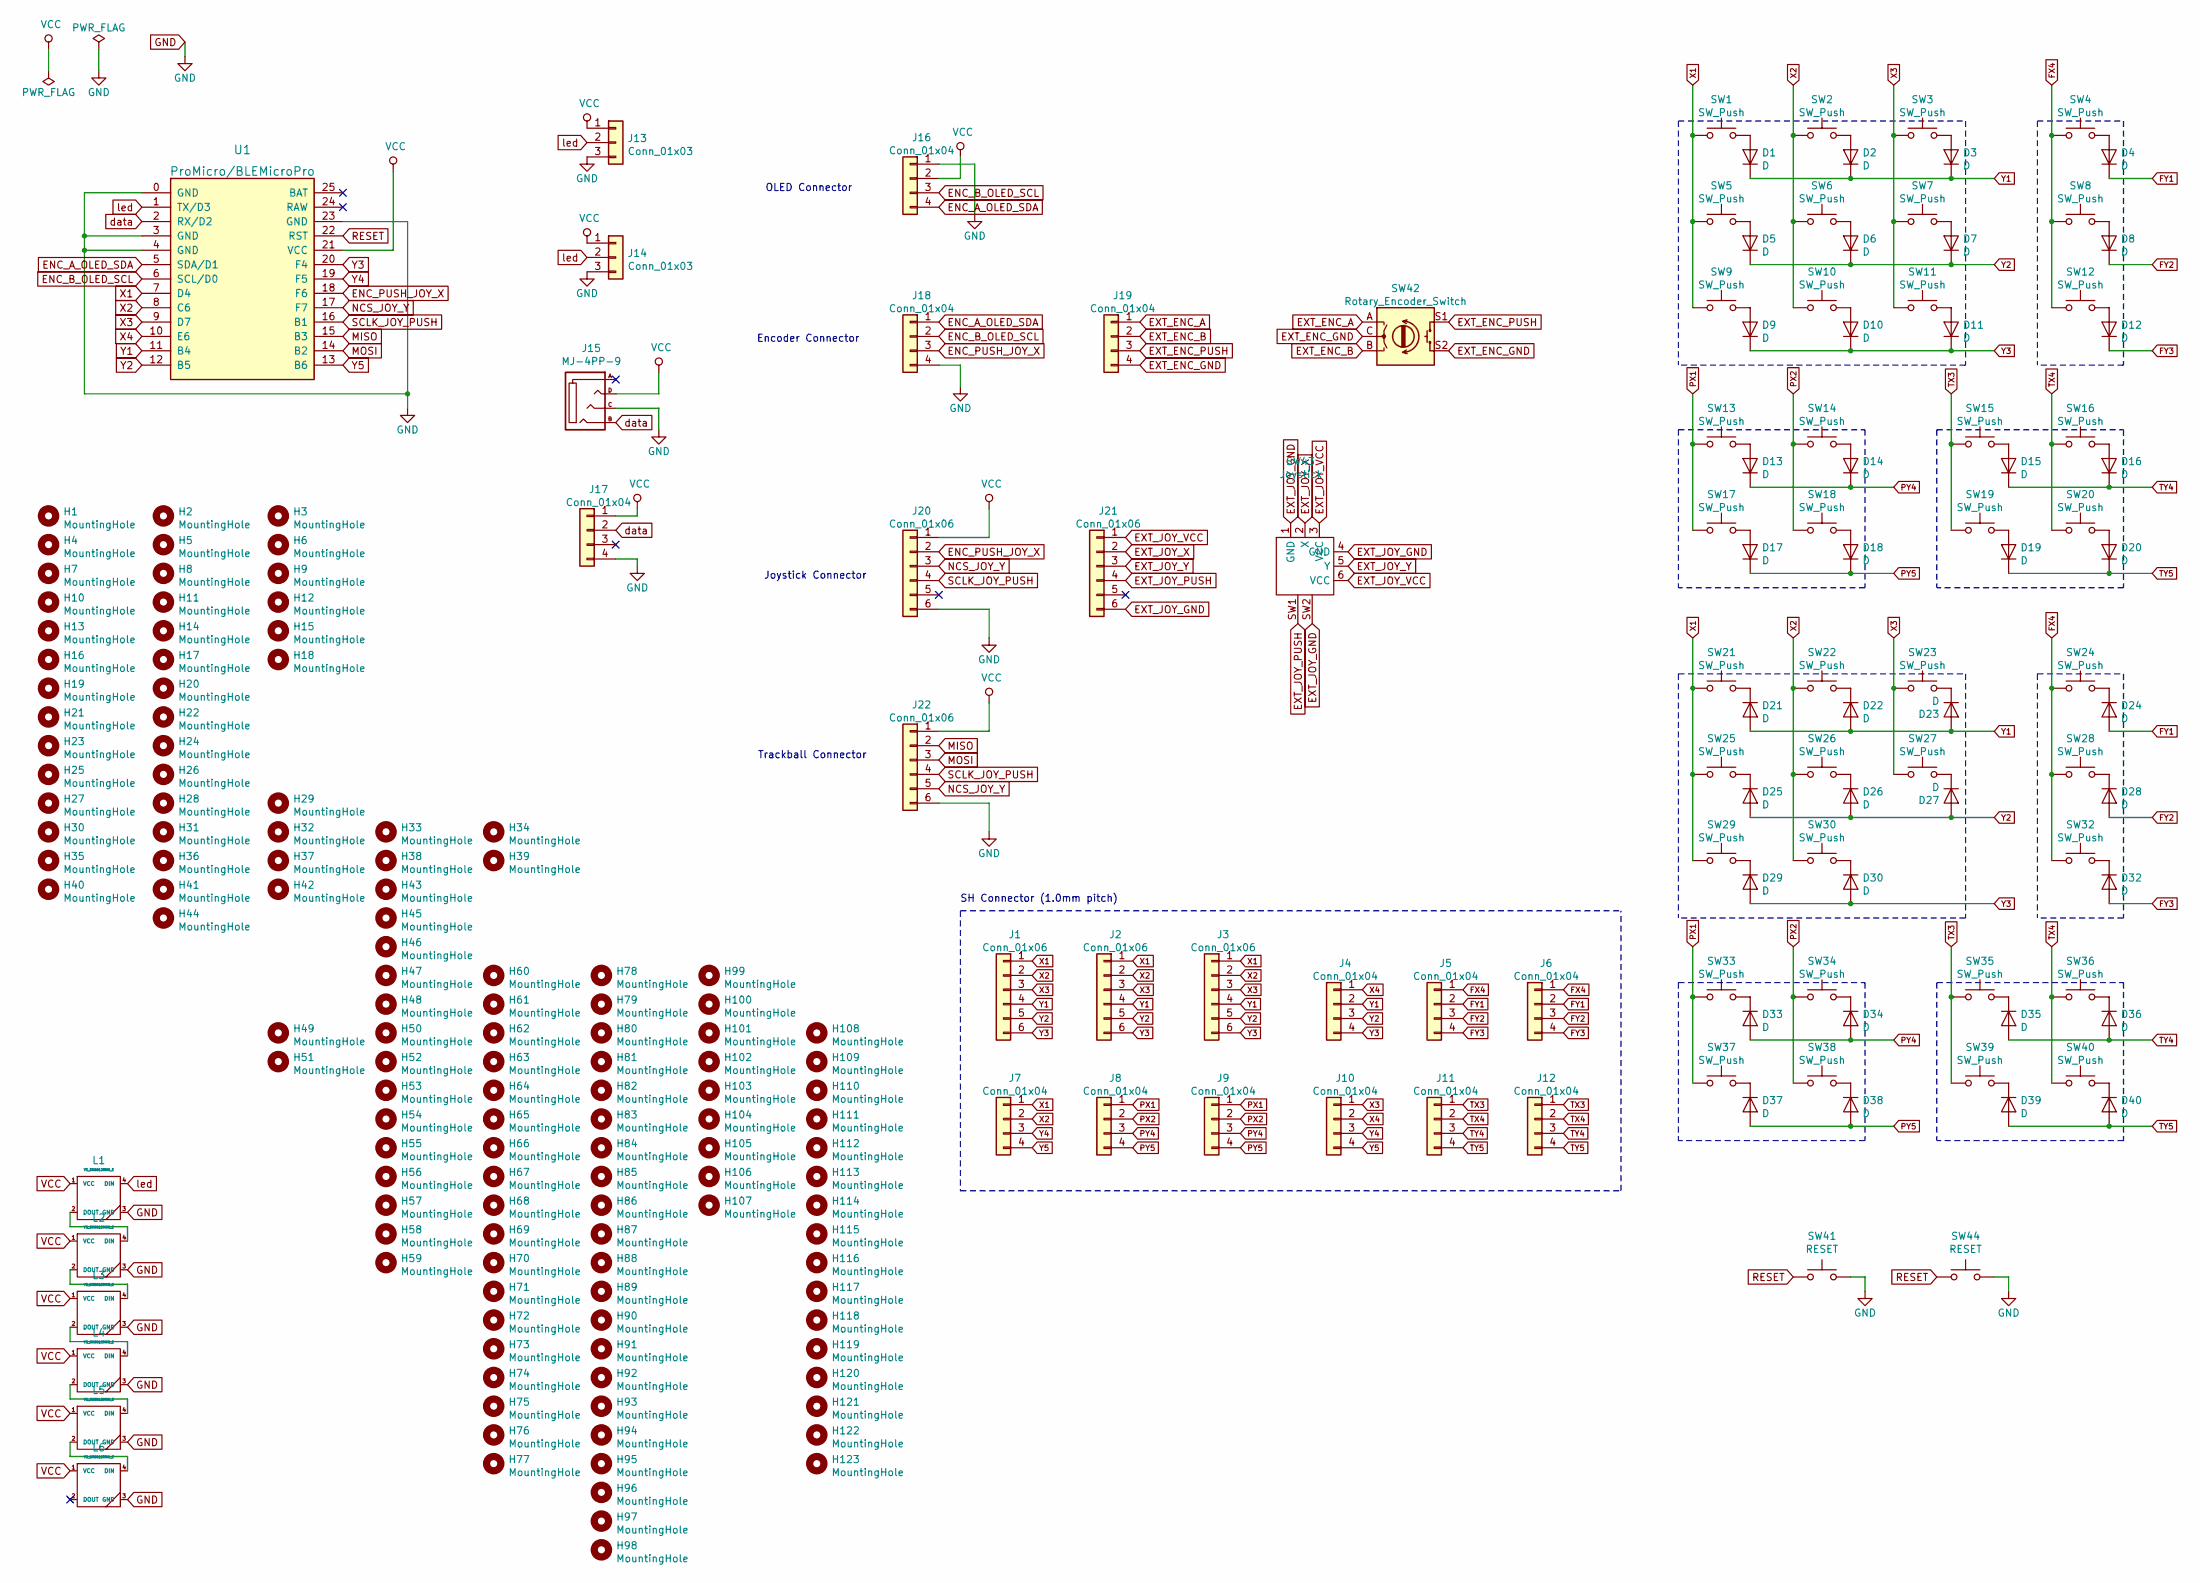
[picture p110: schematic pangaea.kicad_sch]

Parts:
D1, D2, D3, D4, D5, D6, D7, D8, D9, D10, D11, D12, D13, D14, D15, D16, D17, D18, D19, D20, D21, D22, D23, D24, D25, D26, D27, D28, D29, D30, D32, D33, D34, D35, D36, D37, D38, D39, D40: D; diode_TH_SMD_rev3
H1, H2, H3, H4, H5, H6, H7, H8, H9, H10, H11, H12, H13, H14: MountingHole; M2_Nut_Hole_rev2
H15, H16, H17, H18, H19, H26, H27, H28, H29, H30, H31, H32, H33, H34, H35, H36, H37, H38, H39, H40, H41, H42, H43, H44, H45, H46, H47, H48, H49, H50, H51, H52, H53, H54, H55, H56, H57, H58, H59, H60, H61, H62, H63, H78, H79, H80, H81, H82, H83, H84, H99, H100, H101, H102, H103, H104, H105, H106, H107, H108, H109, H110, H111, H112, H113, H114, H115, H116, H117, H118, H119, H120, H121, H122, H123: MountingHole; M1.4_tapping_Hole_rev2
H20, H21, H22, H23, H24, H25: MountingHole; M2_Hole
H64, H65, H66, H67, H68, H85, H86, H87, H88, H89, H90, H91, H92, H93, H94: MountingHole; Slit
H69, H70, H71, H72, H73, H74, H95, H96, H97, H98: MountingHole; Slitb_b
H75, H76, H77: MountingHole; Slitb_c
J1, J2, J3, J20, J21, J22: Conn_01x06; JST_SH_BM03B-SRSS-TB_1x06-1MP_P1.00mm_Vertical
J4, J5, J6, J7, J8, J9, J10, J11, J12, J18, J19: Conn_01x04; JST_SH_BM03B-SRSS-TB_1x04-1MP_P1.00mm_Vertical
J13, J14: Conn_01x03; PinHeader_1x03_P2.54mm_Vertical
J15: MJ-4PP-9
J16: Conn_01x04; PinHeader_1x04_P2.54mm_Vertical
J17: Conn_01x04; JST_SH_BM03B-SRSS-TB_1x04-1MP_P1.00mm_Vertical_onefoot
L1, L2, L3, L4, L5, L6: YS_SK6812MINI_E; YS-SK6812MINI-E
SW1, SW2, SW3, SW4, SW5, SW6, SW7, SW8, SW9, SW10, SW11, SW12, SW13, SW14, SW15, SW16, SW17, SW18, SW19, SW20, SW21, SW22, SW23, SW24, SW25, SW26, SW27, SW28, SW29, SW30, SW32, SW33, SW34, SW35, SW36, SW37, SW38, SW39, SW40: SW_Push; CherryMX_Choc_Hotswap_rev9_test
SW41: RESET; ResetSW
SW42: Rotary_Encoder_Switch; RotaryEncoder_Alps_EC11E-Switch_Vertical_H20mm_rev2
SW43: Joystick; Joystick_AE-RKJXV122400R
SW44: RESET; ResetSW_SidePush
U1: ProMicro/BLEMicroPro; ArduinoProMicro_ConThrough_rev2

Connections:
ENC_A_OLED_SDA: J16.4, J18.1, U1.5 (SDA/D1)
ENC_B_OLED_SCL: J16.3, J18.2, U1.6 (SCL/D0)
ENC_PUSH_JOY_X: J18.3, J20.2, U1.18 (F6)
EXT_ENC_A: J19.1, SW42.A
EXT_ENC_B: J19.2, SW42.B
EXT_ENC_GND: J19.4, SW42.C, SW42.S2
EXT_ENC_PUSH: J19.3, SW42.S1
EXT_JOY_GND: J21.6, SW43.1 (GND), SW43.4 (GND), SW43.SW2
EXT_JOY_PUSH: J21.4, SW43.SW1
EXT_JOY_VCC: J21.1, SW43.3 (VCC), SW43.6 (VCC)
EXT_JOY_X: J21.2, SW43.2 (X)
EXT_JOY_Y: J21.3, SW43.5 (Y)
FX4: J5.1, J6.1, SW4.1, SW8.1, SW12.1, SW24.1, SW28.1, SW32.1
FY1: D4.1 (K), D24.2 (A), J5.2, J6.2
FY2: D8.1 (K), D28.2 (A), J5.3, J6.3
FY3: D12.1 (K), D32.2 (A), J5.4, J6.4
GND: J13.3, J14.3, J15.C, J16.1, J17.4, J18.4, J20.6, J22.6, L1.3 (GND), L2.3 (GND), L3.3 (GND), L4.3 (GND), L5.3 (GND), L6.3 (GND), SW41.2, SW44.2, U1.0 (GND), U1.3 (GND), U1.4 (GND), U1.23 (GND)
MISO: J22.2, U1.15 (B3)
MOSI: J22.3, U1.14 (B2)
NCS_JOY_Y: J20.3, J22.5, U1.17 (F7)
unnamed: D1.2 (A), SW1.2
unnamed: D2.2 (A), SW2.2
unnamed: D3.2 (A), SW3.2
unnamed: D4.2 (A), SW4.2
unnamed: D5.2 (A), SW5.2
unnamed: D6.2 (A), SW6.2
unnamed: D7.2 (A), SW7.2
unnamed: D8.2 (A), SW8.2
unnamed: D9.2 (A), SW9.2
unnamed: D10.2 (A), SW10.2
unnamed: D11.2 (A), SW11.2
unnamed: D12.2 (A), SW12.2
unnamed: D13.2 (A), SW13.2
unnamed: D14.2 (A), SW14.2
unnamed: D15.2 (A), SW15.2
unnamed: D16.2 (A), SW16.2
unnamed: D17.2 (A), SW17.2
unnamed: D18.2 (A), SW18.2
unnamed: D19.2 (A), SW19.2
unnamed: D20.2 (A), SW20.2
unnamed: D21.1 (K), SW21.2
unnamed: D22.1 (K), SW22.2
unnamed: D23.1 (K), SW23.2
unnamed: D24.1 (K), SW24.2
unnamed: D25.1 (K), SW25.2
unnamed: D26.1 (K), SW26.2
unnamed: D27.1 (K), SW27.2
unnamed: D28.1 (K), SW28.2
unnamed: D29.1 (K), SW29.2
unnamed: D30.1 (K), SW30.2
unnamed: D32.1 (K), SW32.2
unnamed: D33.1 (K), SW33.2
unnamed: D34.1 (K), SW34.2
unnamed: D35.1 (K), SW35.2
unnamed: D36.1 (K), SW36.2
unnamed: D37.1 (K), SW37.2
unnamed: D38.1 (K), SW38.2
unnamed: D39.1 (K), SW39.2
unnamed: D40.1 (K), SW40.2
unnamed: L1.2 (DOUT), L2.4 (DIN)
unnamed: L2.2 (DOUT), L3.4 (DIN)
unnamed: L3.2 (DOUT), L4.4 (DIN)
unnamed: L4.2 (DOUT), L5.4 (DIN)
unnamed: L5.2 (DOUT), L6.4 (DIN)
PX1: J8.1, J9.1, SW13.1, SW17.1, SW33.1, SW37.1
PX2: J8.2, J9.2, SW14.1, SW18.1, SW34.1, SW38.1
PY4: D13.1 (K), D14.1 (K), D33.2 (A), D34.2 (A), J8.3, J9.3
PY5: D17.1 (K), D18.1 (K), D37.2 (A), D38.2 (A), J8.4, J9.4
RESET: SW41.1, SW44.1, U1.22 (RST)
SCLK_JOY_PUSH: J20.4, J22.4, U1.16 (B1)
TX3: J11.1, J12.1, SW15.1, SW19.1, SW35.1, SW39.1
TX4: J11.2, J12.2, SW16.1, SW20.1, SW36.1, SW40.1
TY4: D15.1 (K), D16.1 (K), D35.2 (A), D36.2 (A), J11.3, J12.3
TY5: D19.1 (K), D20.1 (K), D39.2 (A), D40.2 (A), J11.4, J12.4
VCC: J13.1, J14.1, J15.D, J16.2, J17.1, J20.1, J22.1, L1.1 (VCC), L2.1 (VCC), L3.1 (VCC), L4.1 (VCC), L5.1 (VCC), L6.1 (VCC), U1.21 (VCC)
X1: J1.1, J2.1, J3.1, J7.1, SW1.1, SW5.1, SW9.1, SW21.1, SW25.1, SW29.1, U1.7 (D4)
X2: J1.2, J2.2, J3.2, J7.2, SW2.1, SW6.1, SW10.1, SW22.1, SW26.1, SW30.1, U1.8 (C6)
X3: J1.3, J2.3, J3.3, J10.1, SW3.1, SW7.1, SW11.1, SW23.1, SW27.1, U1.9 (D7)
X4: J4.1, J10.2, U1.10 (E6)
Y1: D1.1 (K), D2.1 (K), D3.1 (K), D21.2 (A), D22.2 (A), D23.2 (A), J1.4, J2.4, J3.4, J4.2, U1.11 (B4)
Y2: D5.1 (K), D6.1 (K), D7.1 (K), D25.2 (A), D26.2 (A), D27.2 (A), J1.5, J2.5, J3.5, J4.3, U1.12 (B5)
Y3: D9.1 (K), D10.1 (K), D11.1 (K), D29.2 (A), D30.2 (A), J1.6, J2.6, J3.6, J4.4, U1.20 (F4)
Y4: J7.3, J10.3, U1.19 (F5)
Y5: J7.4, J10.4, U1.13 (B6)
data: J15.B, J17.2, U1.2 (RX/D2)
led: J13.2, J14.2, L1.4 (DIN), U1.1 (TX/D3)

Notes on the sheet:
OLED Connector
Encoder Connector
Joystick Connector
Trackball Connector
SH Connector (1.0mm pitch)
