e3w2q/Pangaea-keyboard/firmware/pangaea/keymaps/vial/config.h

#pragma once

#define VIAL_KEYBOARD_UID {0xBD, 0xC1, 0xB8, 0x2B, 0xE0, 0xAA, 0xF2, 0xB9}
#define VIAL_UNLOCK_COMBO_ROWS {0, 3}
#define VIAL_UNLOCK_COMBO_COLS {3, 5}

#define DYNAMIC_KEYMAP_LAYER_COUNT 3

#undef LOCKING_SUPPORT_ENABLE
#undef LOCKING_RESYNC_ENABLE

#define LAYER_STATE_8BIT
#define NO_ACTION_TAPPING
#define NO_ACTION_ONESHOT
#define NO_MUSIC_MODE

#undef RGBLIGHT_EFFECT_ALTERNATING
#undef RGBLIGHT_EFFECT_CHRISTMAS
#undef RGBLIGHT_EFFECT_RGB_TEST
#undef RGBLIGHT_EFFECT_SNAKE
#undef RGBLIGHT_EFFECT_STATIC_GRADIENT
